and3rson/lilka/docs/keira/lua/reference/lilka.rst

``lilka``: Спеціальні функції
=============================

Цей модуль описує функції, які ви можете визначити в своєму коді, щоб вони викликались автоматично в певних ситуаціях.

Детальніше про їх поведінку можна прочитати в :ref:`секції про написання ігор на Lua <lua-games>`.

.. lua:module:: lilka
    :noindex:

.. lua:function:: init()

    Ця функція автоматично викликається один раз при запуску програми.

    Ви повинні визначити її в своєму коді, якщо ви хочете використовувати її для ініціалізації вашої програми.

.. lua:function:: update(delta)

    :type delta: number
    :param delta: Час, який пройшов з останнього кадру.

    Ця функція автоматично викликається кожен кадр. Тут виконується ігрова логіка. В параметрі delta передається час, який пройшов з останнього кадру.

    Ви повинні визначити її в своєму коді, якщо ви хочете використовувати її для оновлення вашої програми.

.. lua:function:: draw()

    Ця функція автоматично викликається після `lilka.update`. Тут відбувається відображення графіки.

    Ви повинні визначити її в своєму коді, якщо ви хочете використовувати її для малювання вашої програми.

.. lua:autoclass:: lilka

    .. Does not work with aliases... So we have to copy-paste the stuff above.
    .. :members: init, update, draw
