and3rson/lilka/docs/keira/lua/reference/buzzer.rst

``buzzer`` - П'єзо-динамік
--------------------------

Функції для роботи з п'єзо-динаміком.

.. note:: Ці функції не блокують виконання програми: всі звуки та мелодії відтворюються в фоновому режимі.

.. lua:autoclass:: buzzer
