and3rson/lilka/docs/keira/lua/reference/math.rst

``math`` - Арифметичні функції
------------------------------

Цей модуль містить функції для виконання різних арифметичних та тригонометричних операцій.

.. lua:autoclass:: math
