and3rson/lilka/docs/keira/lua/reference/geometry.rst

``geometry`` - Геометричні функції
----------------------------------

Цей модуль містить функції, які будуть корисні для створення ігор, де потрібно працювати з геометричними об'єктами та колізіями.

.. lua:autoclass:: geometry
