and3rson/lilka/docs/keira/lua/reference/state.rst

``state`` - Збереження стану програми
-------------------------------------

.. lua:autoclass:: state
