and3rson/lilka/docs/keira/lua/reference/util.rst

``util`` - Утиліти
------------------

Різні корисні функції.

.. lua:autoclass:: util
