and3rson/lilka/docs/_static/lilka_bottom.png

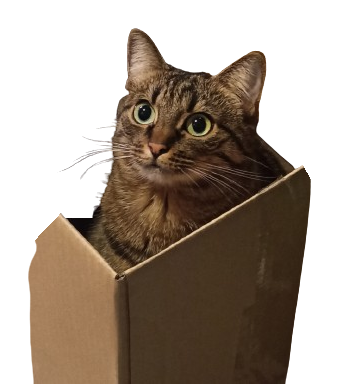
docs/_static/lilka_bottom.png
