and3rson/lilka/docs/_static/lilka_bottom_20.png

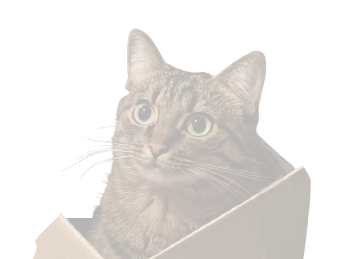
docs/_static/lilka_bottom_20.png
