and3rson/lilka/docs/_static/v2.jpg

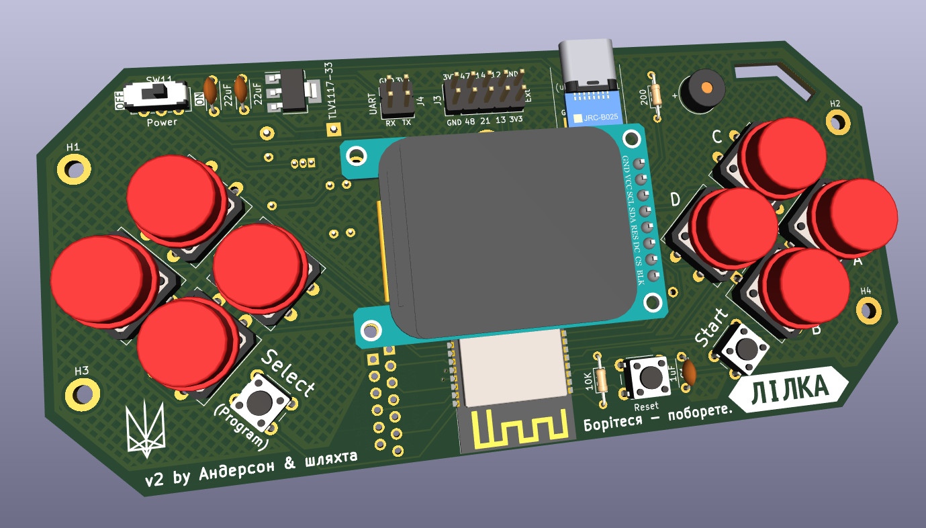
docs/_static/v2.jpg
