and3rson/lilka/docs/keira/images/02_inside_vscode.png

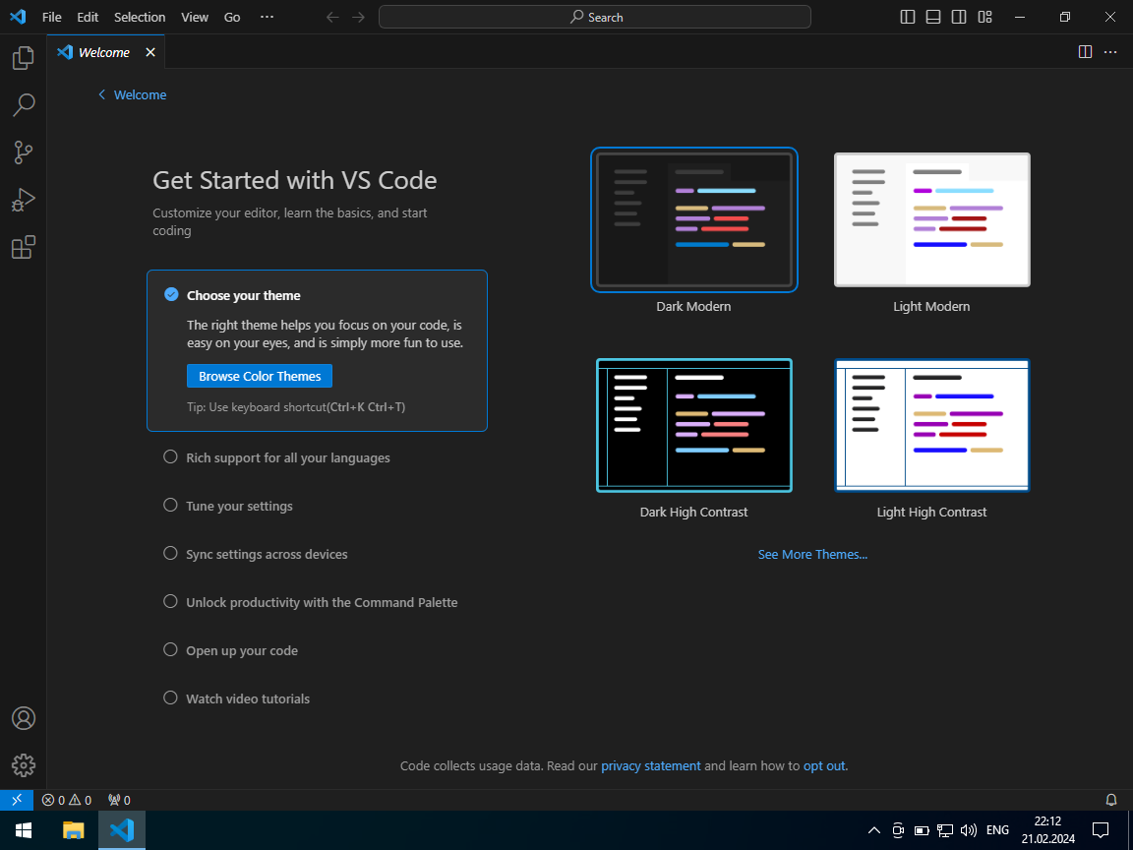
docs/keira/images/02_inside_vscode.png
