and3rson/lilka/docs/keira/images/08_clone_repo.png

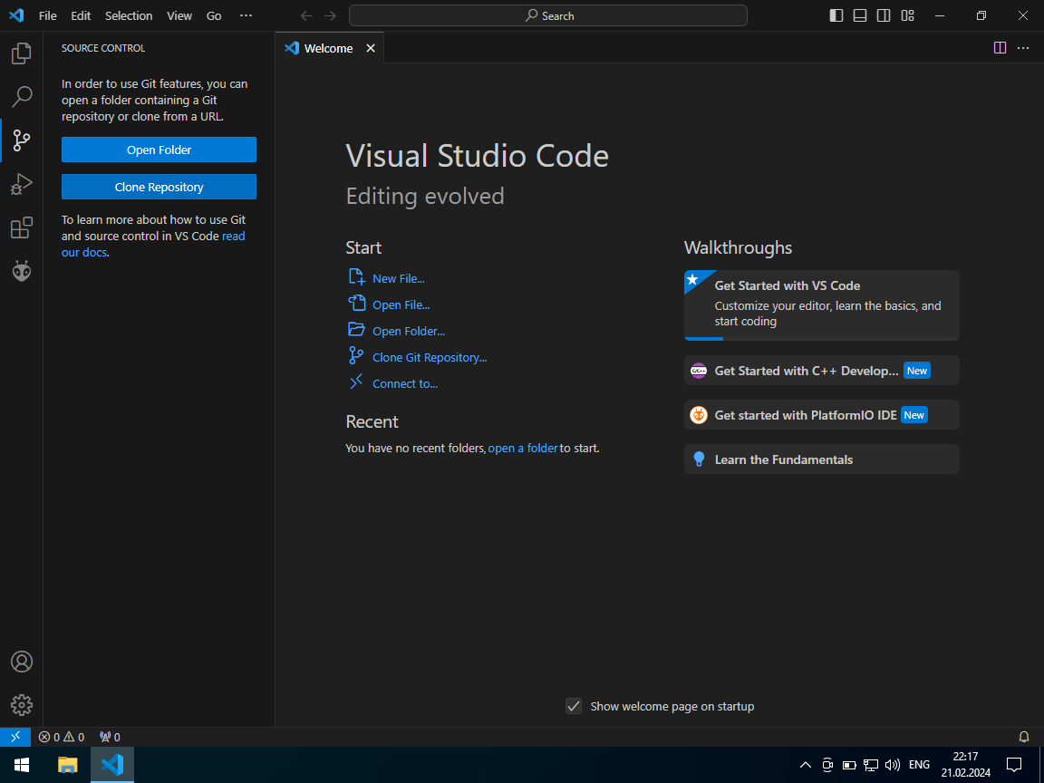
docs/keira/images/08_clone_repo.png
