and3rson/lilka/docs/keira/images/10_see_cloned_repo.png

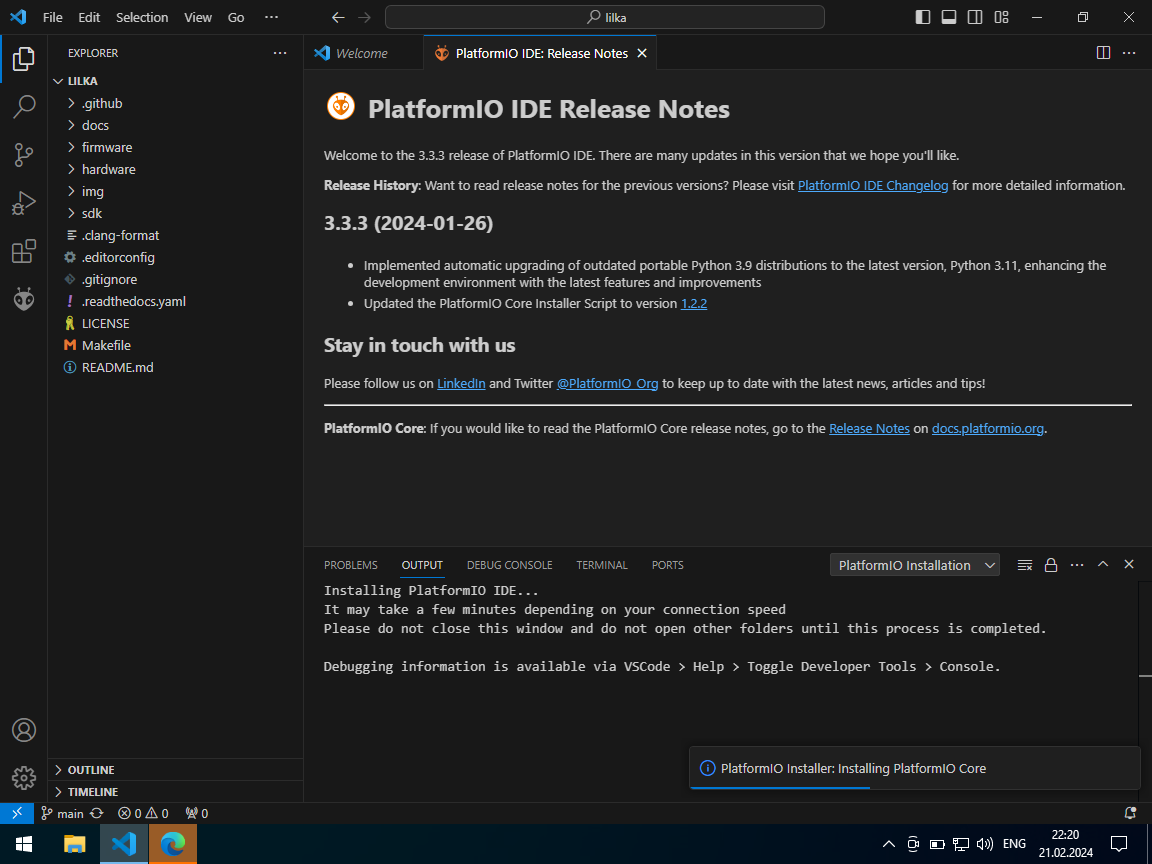
docs/keira/images/10_see_cloned_repo.png
