and3rson/lilka/docs/keira/images/11_open_pio_project.png

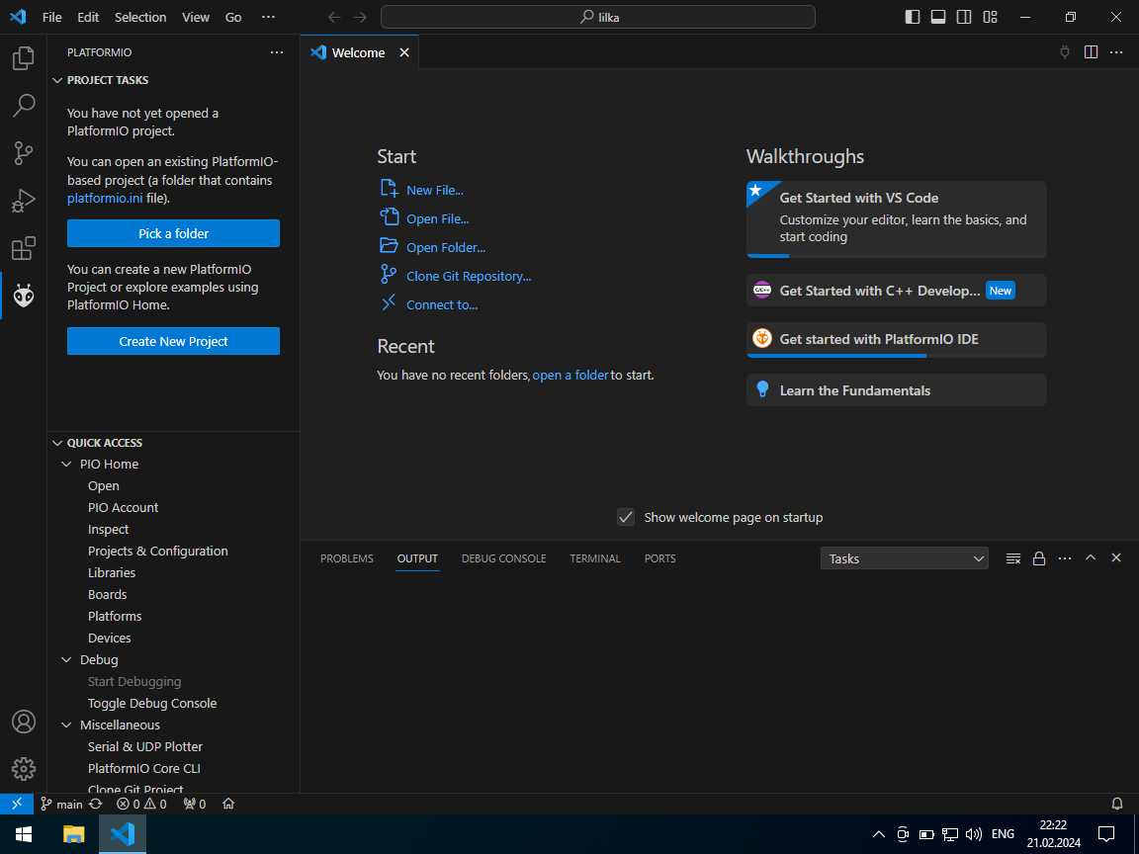
docs/keira/images/11_open_pio_project.png
