and3rson/lilka/docs/keira/images/12_wait_pio_project_init.png

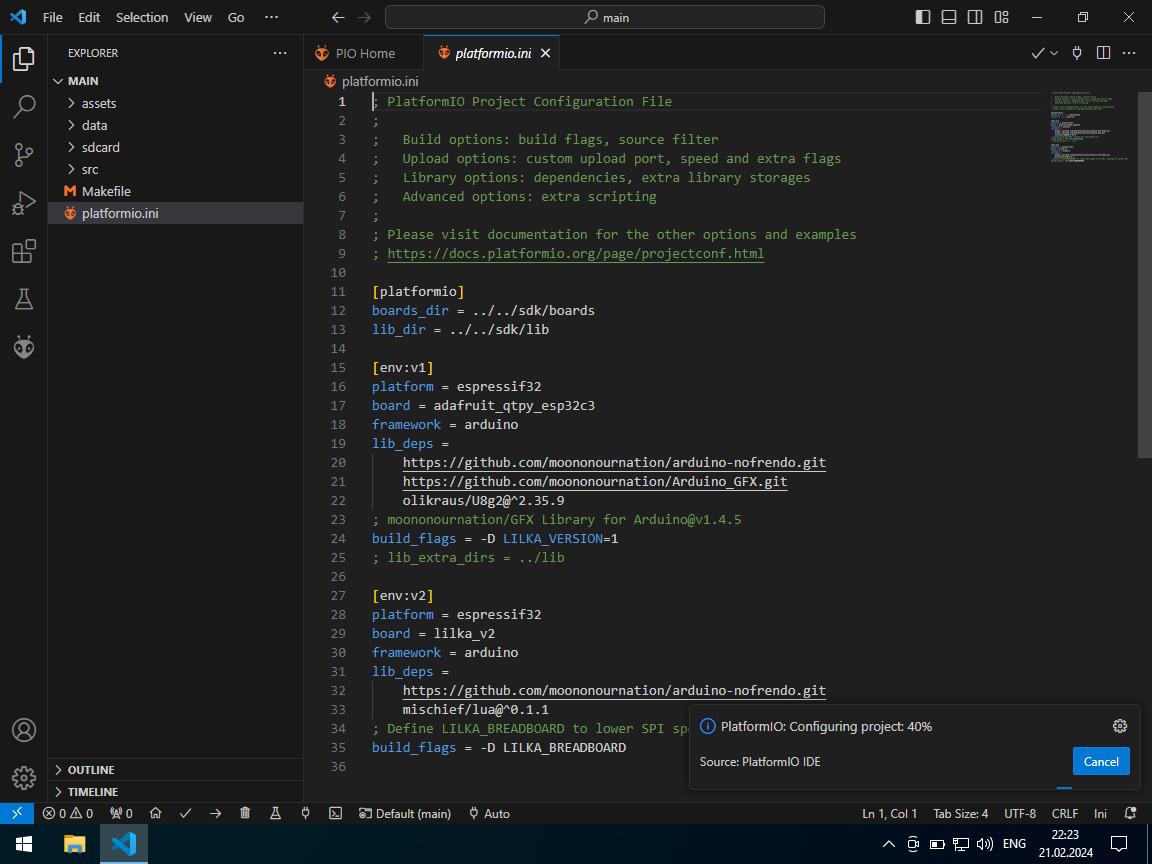
docs/keira/images/12_wait_pio_project_init.png
