and3rson/lilka/docs/keira/images/13_wait_pio_project_init_more.png

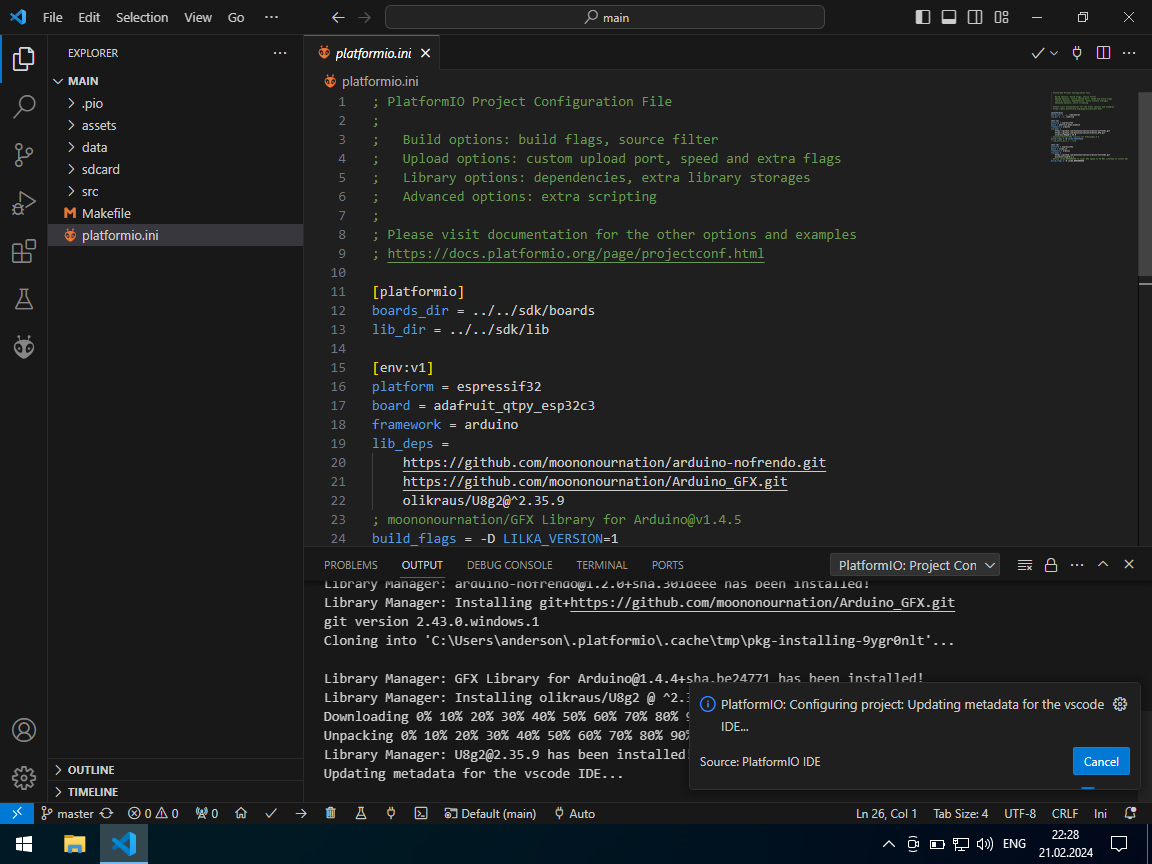
docs/keira/images/13_wait_pio_project_init_more.png
