and3rson/lilka/docs/keira/images/17_run_upload_v2.png

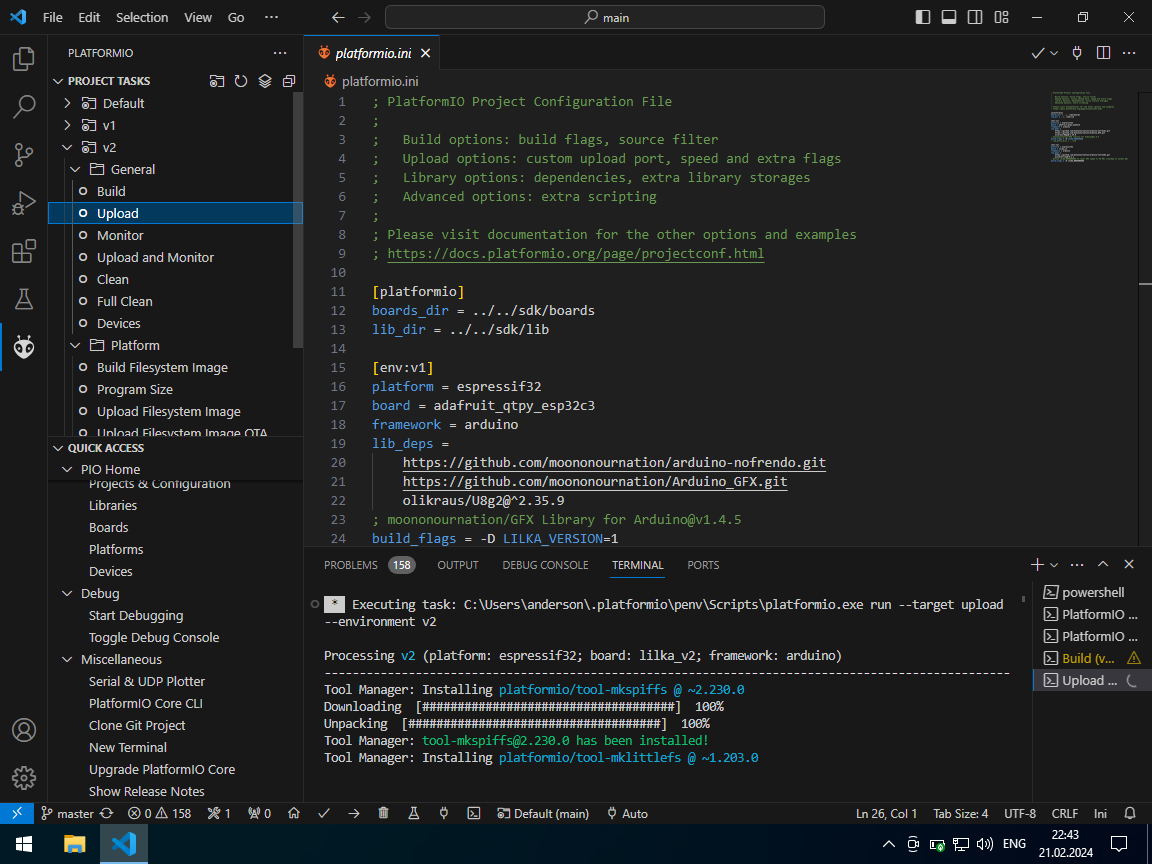
docs/keira/images/17_run_upload_v2.png
