and3rson/lilka/docs/keira/images/18_upload_progress.png

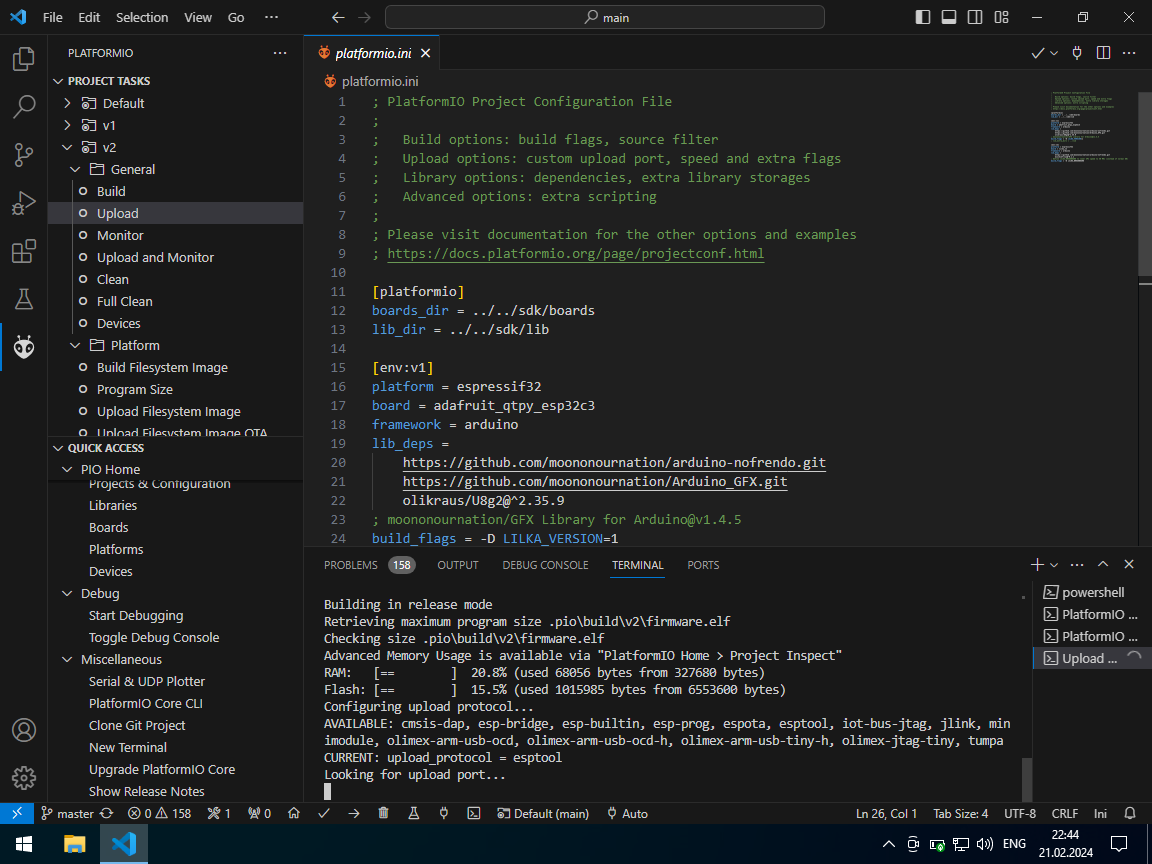
docs/keira/images/18_upload_progress.png
