and3rson/lilka/docs/programming/images/01_download_vscode.png

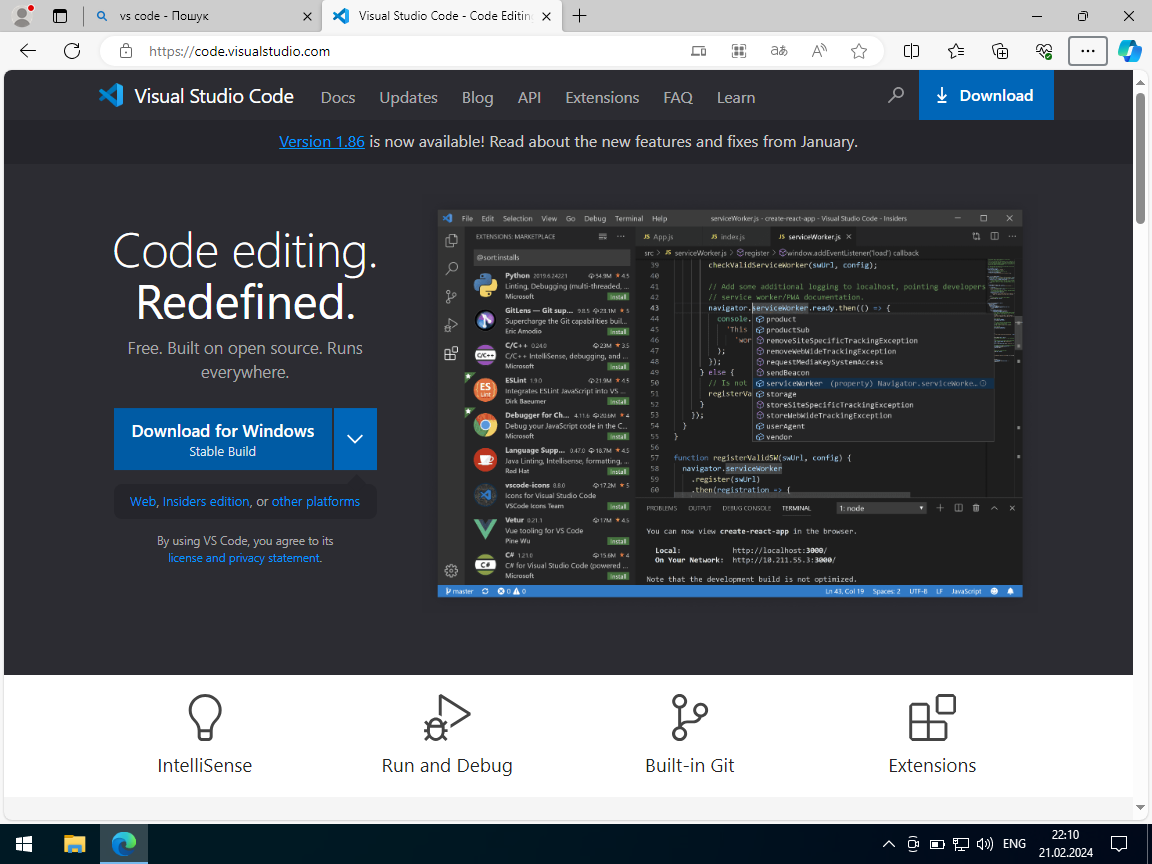
docs/programming/images/01_download_vscode.png
