and3rson/lilka/docs/programming/images/07_use_vs_code_with_git.png

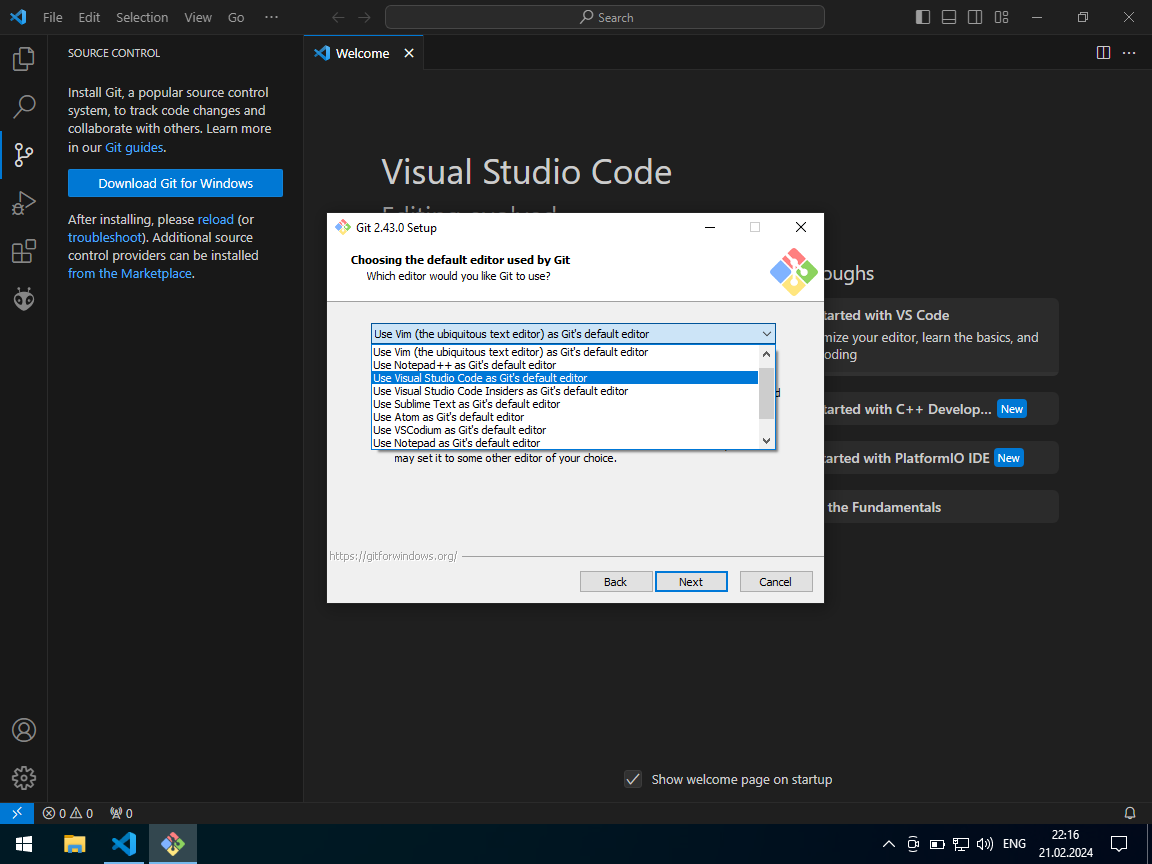
docs/programming/images/07_use_vs_code_with_git.png
