and3rson/lilka/docs/programming/images/custom_firmware/01_pio_new_proj.png

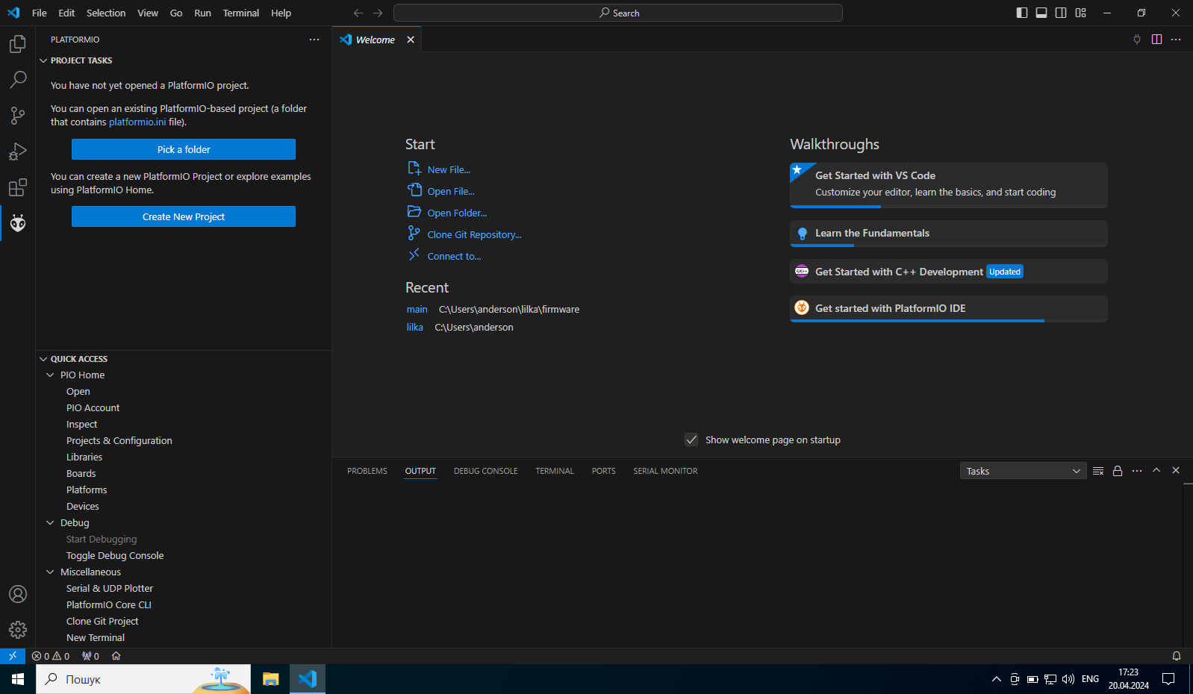
docs/programming/images/custom_firmware/01_pio_new_proj.png
