and3rson/lilka/docs/programming/images/custom_firmware/09_lilka_begin.png

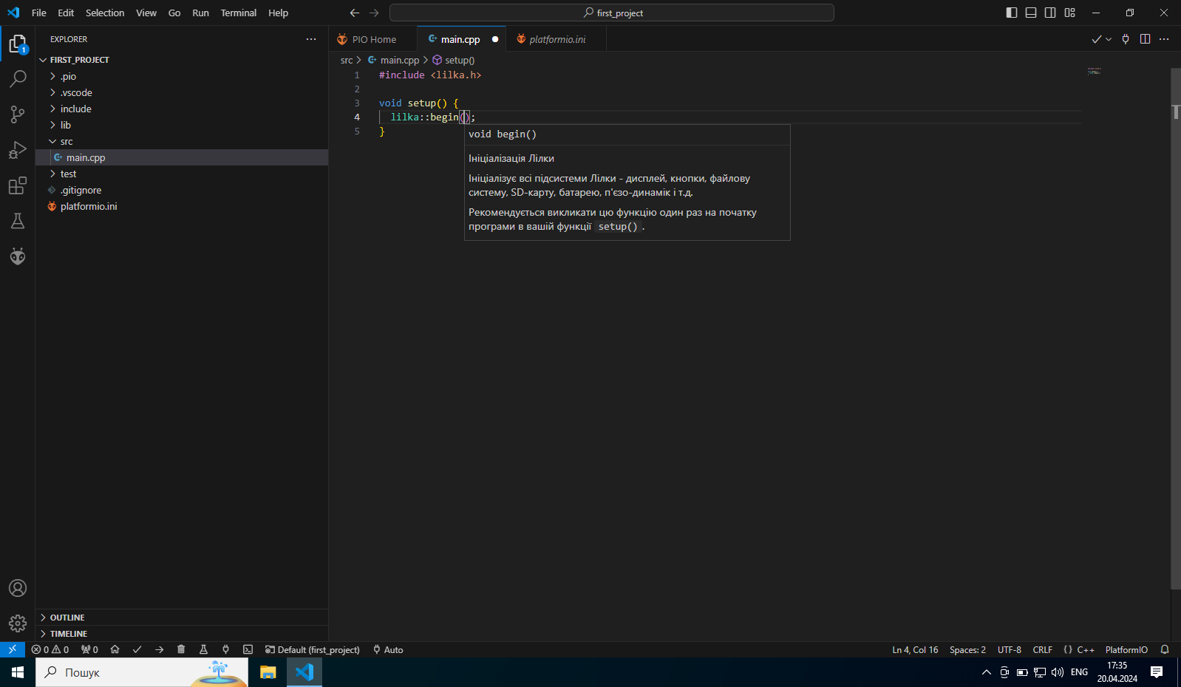
docs/programming/images/custom_firmware/09_lilka_begin.png
