and3rson/lilka/firmware/keira/sdcard/cat/both.bmp

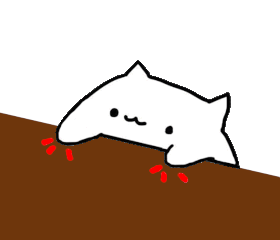
firmware/keira/sdcard/cat/both.bmp
