and3rson/lilka/firmware/keira/sdcard/cat/right.bmp

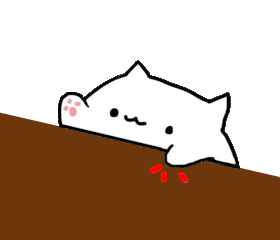
firmware/keira/sdcard/cat/right.bmp
