and3rson/lilka/img/main.png

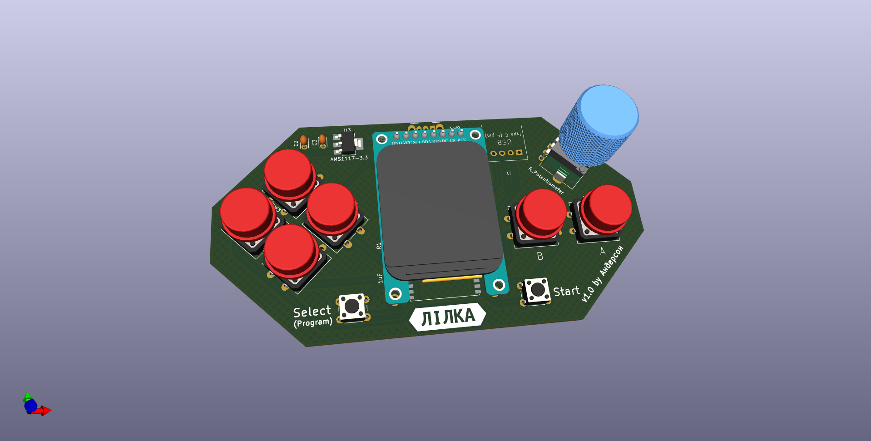
img/main.png
