and3rson/lilka/docs/assembly/images/parts/1n4001.jpg

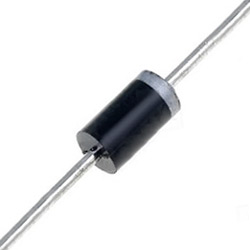
docs/assembly/images/parts/1n4001.jpg
