and3rson/lilka/docs/assembly/images/parts/6mm.jpg

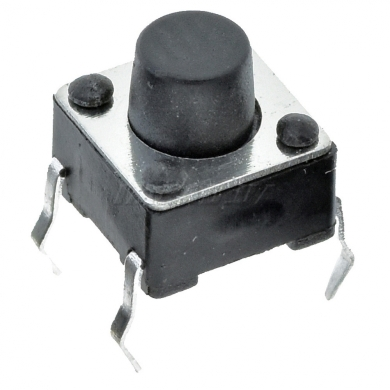
docs/assembly/images/parts/6mm.jpg
