and3rson/lilka/docs/assembly/images/parts/12mm.jpg

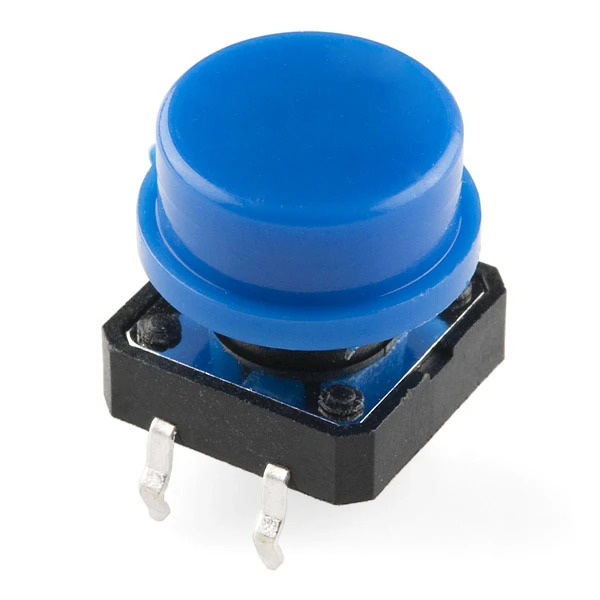
docs/assembly/images/parts/12mm.jpg
