and3rson/lilka/docs/assembly/images/parts/cap.jpg

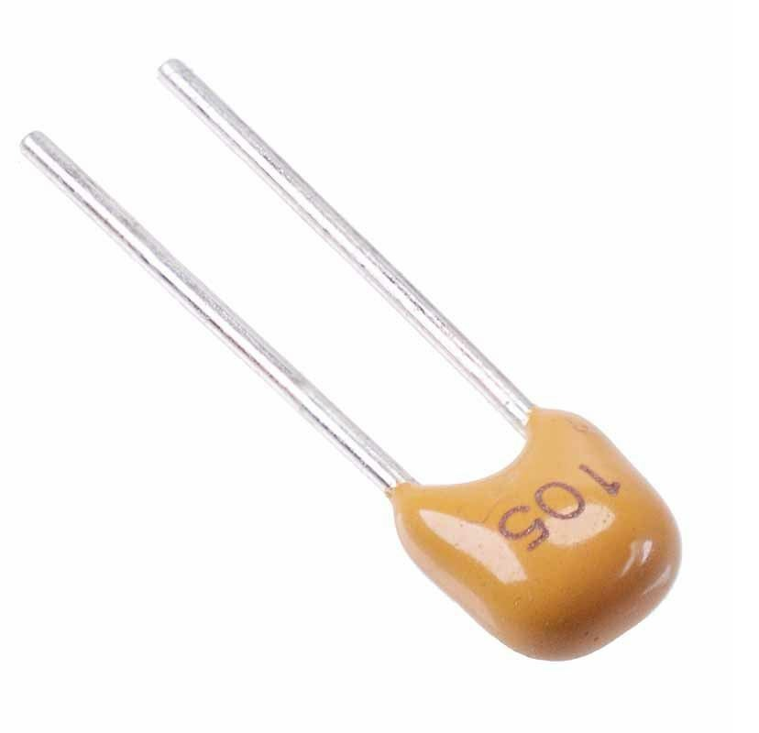
docs/assembly/images/parts/cap.jpg
