and3rson/lilka/docs/assembly/images/parts/display.jpg

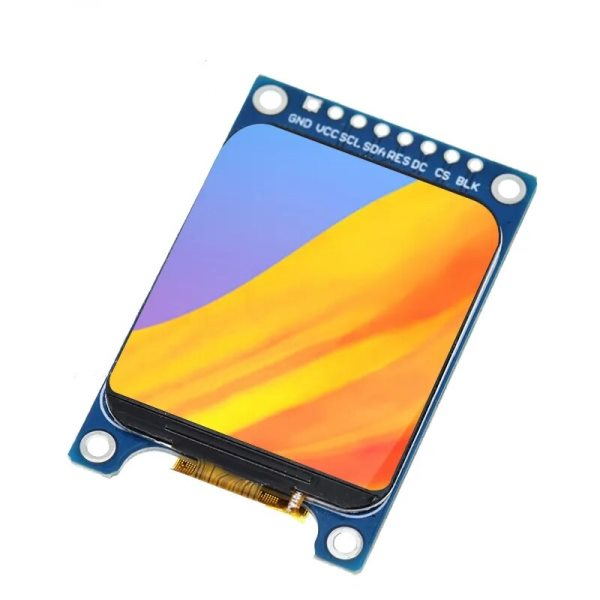
docs/assembly/images/parts/display.jpg
