and3rson/lilka/docs/assembly/images/parts/header.jpg

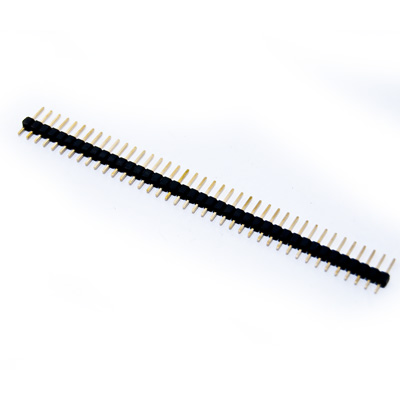
docs/assembly/images/parts/header.jpg
