and3rson/lilka/docs/assembly/images/parts/irlml6401.jpg

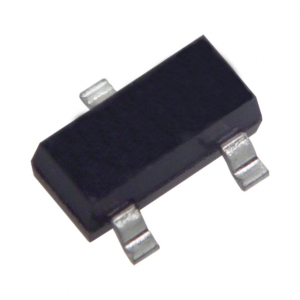
docs/assembly/images/parts/irlml6401.jpg
