and3rson/lilka/docs/assembly/images/parts/lipo.jpg

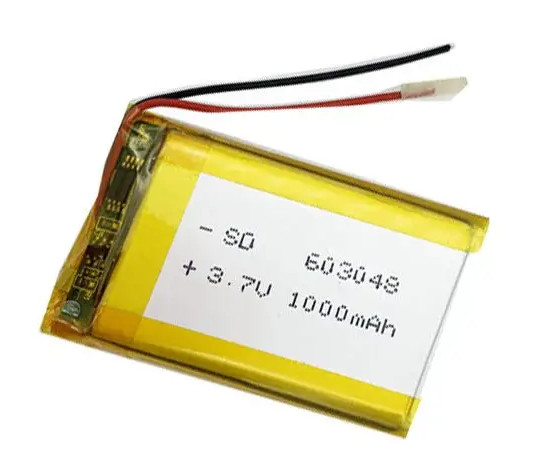
docs/assembly/images/parts/lipo.jpg
