and3rson/lilka/docs/assembly/images/parts/max98357.jpg

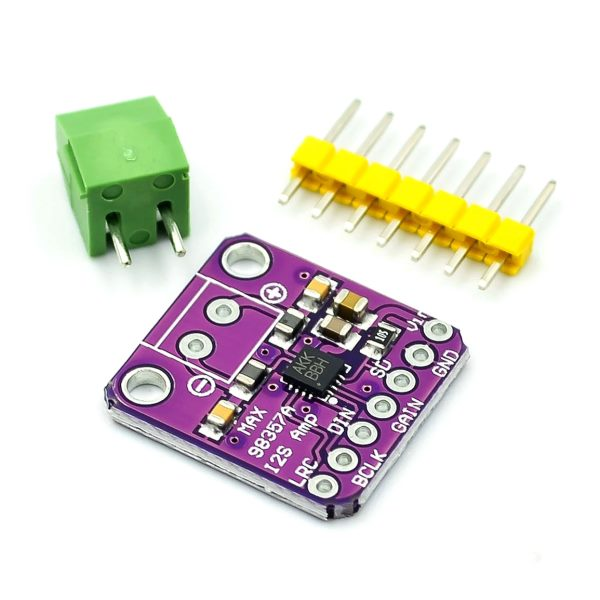
docs/assembly/images/parts/max98357.jpg
