and3rson/lilka/docs/assembly/images/parts/mcu.jpg

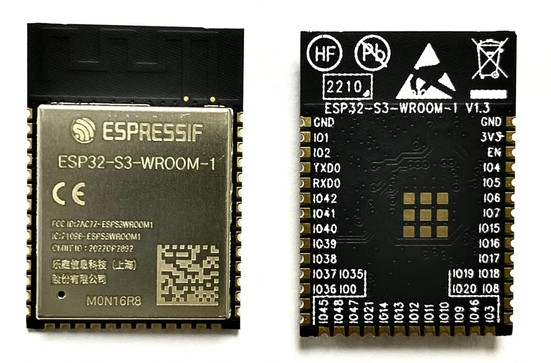
docs/assembly/images/parts/mcu.jpg
