and3rson/lilka/docs/assembly/images/parts/r10k.jpg

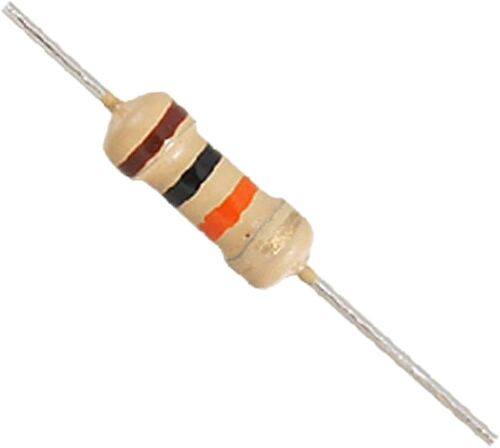
docs/assembly/images/parts/r10k.jpg
