and3rson/lilka/docs/assembly/images/parts/r33k.jpg

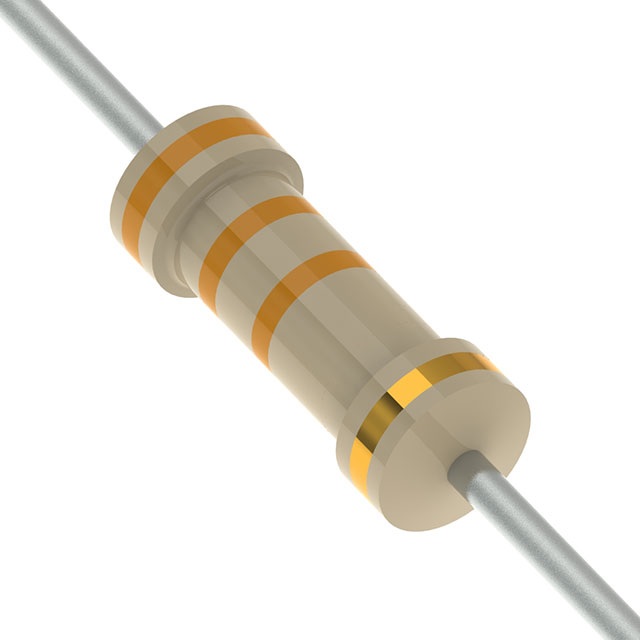
docs/assembly/images/parts/r33k.jpg
