and3rson/lilka/docs/assembly/images/parts/r100k.jpg

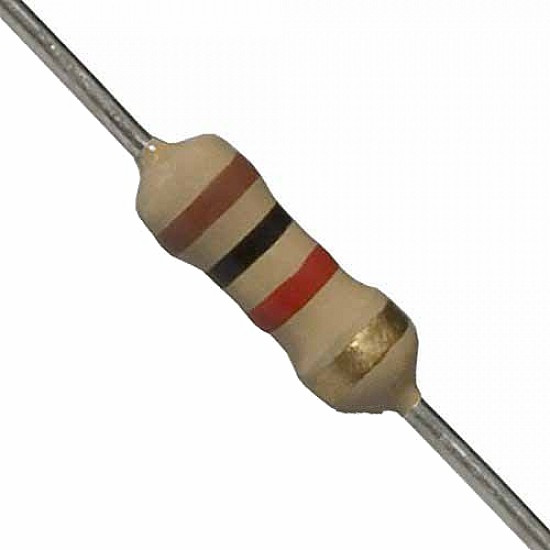
docs/assembly/images/parts/r100k.jpg
