and3rson/lilka/docs/assembly/images/parts/reg.jpg

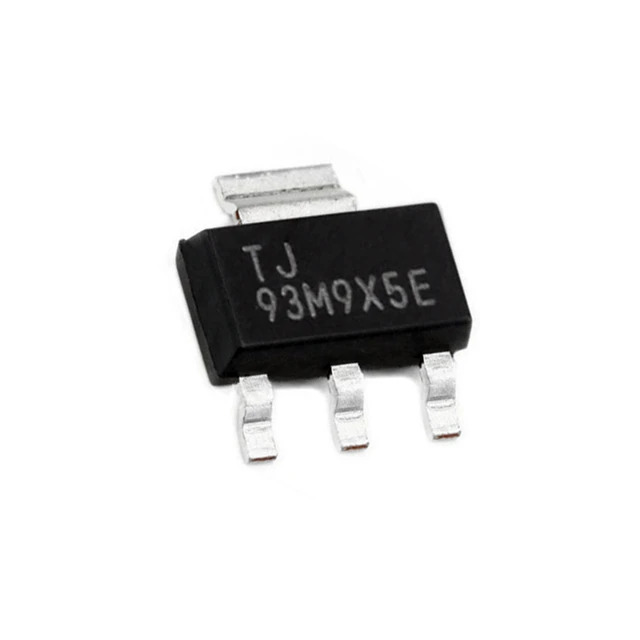
docs/assembly/images/parts/reg.jpg
