and3rson/lilka/docs/assembly/images/parts/sd.jpg

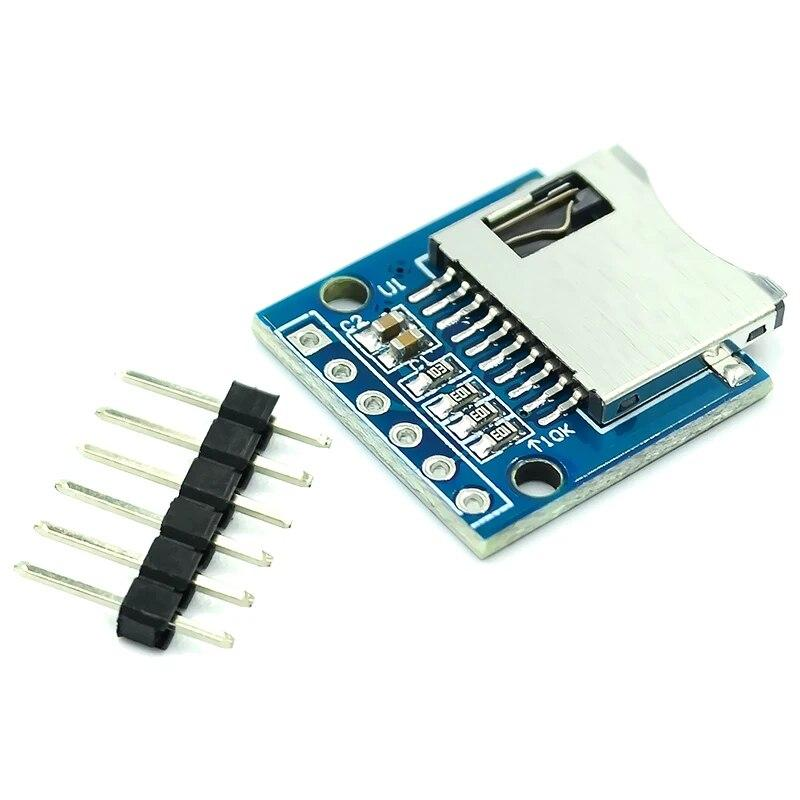
docs/assembly/images/parts/sd.jpg
