and3rson/lilka/docs/assembly/images/parts/socket.jpg

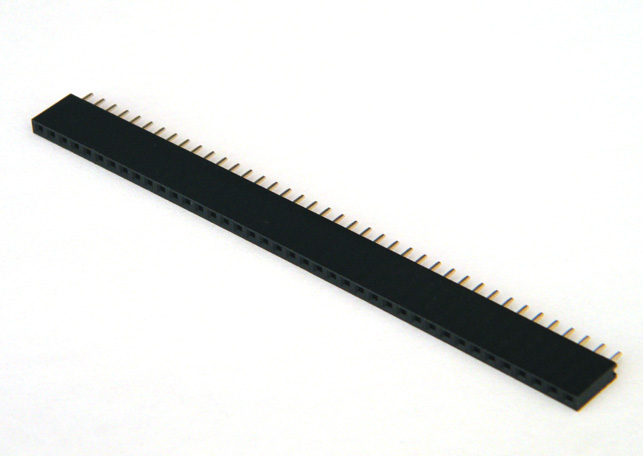
docs/assembly/images/parts/socket.jpg
