and3rson/lilka/docs/assembly/images/parts/speaker.jpg

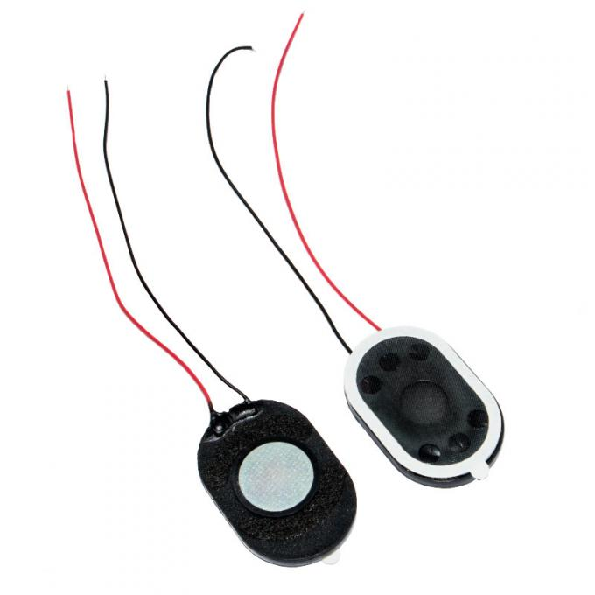
docs/assembly/images/parts/speaker.jpg
