and3rson/lilka/docs/assembly/images/parts/toggle.jpg

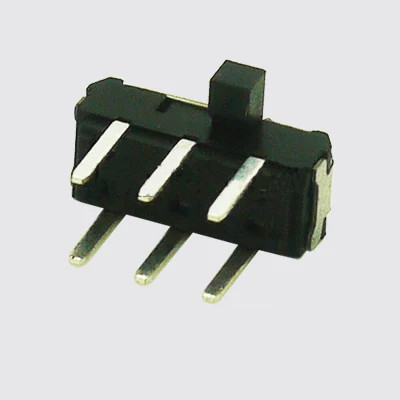
docs/assembly/images/parts/toggle.jpg
