and3rson/lilka/docs/assembly/images/parts/tp4056.jpg

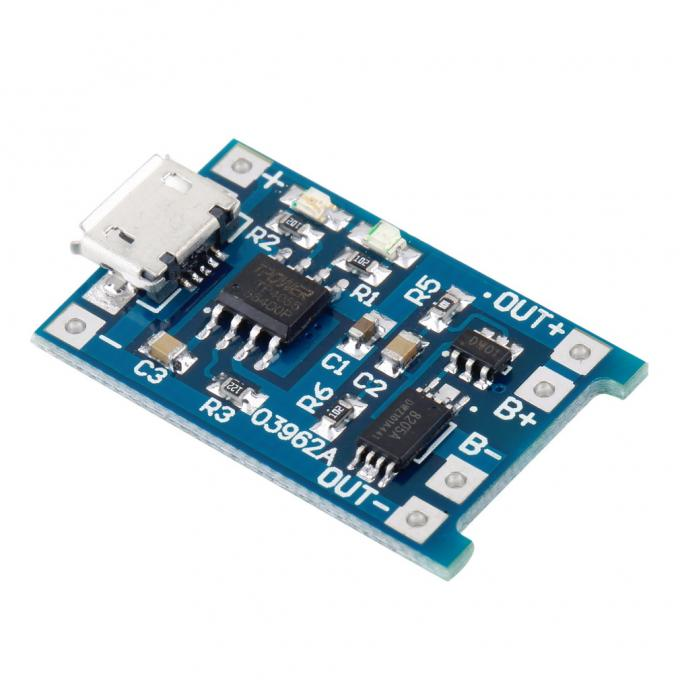
docs/assembly/images/parts/tp4056.jpg
