and3rson/lilka/docs/keira/images/14_pio_build_v2.png

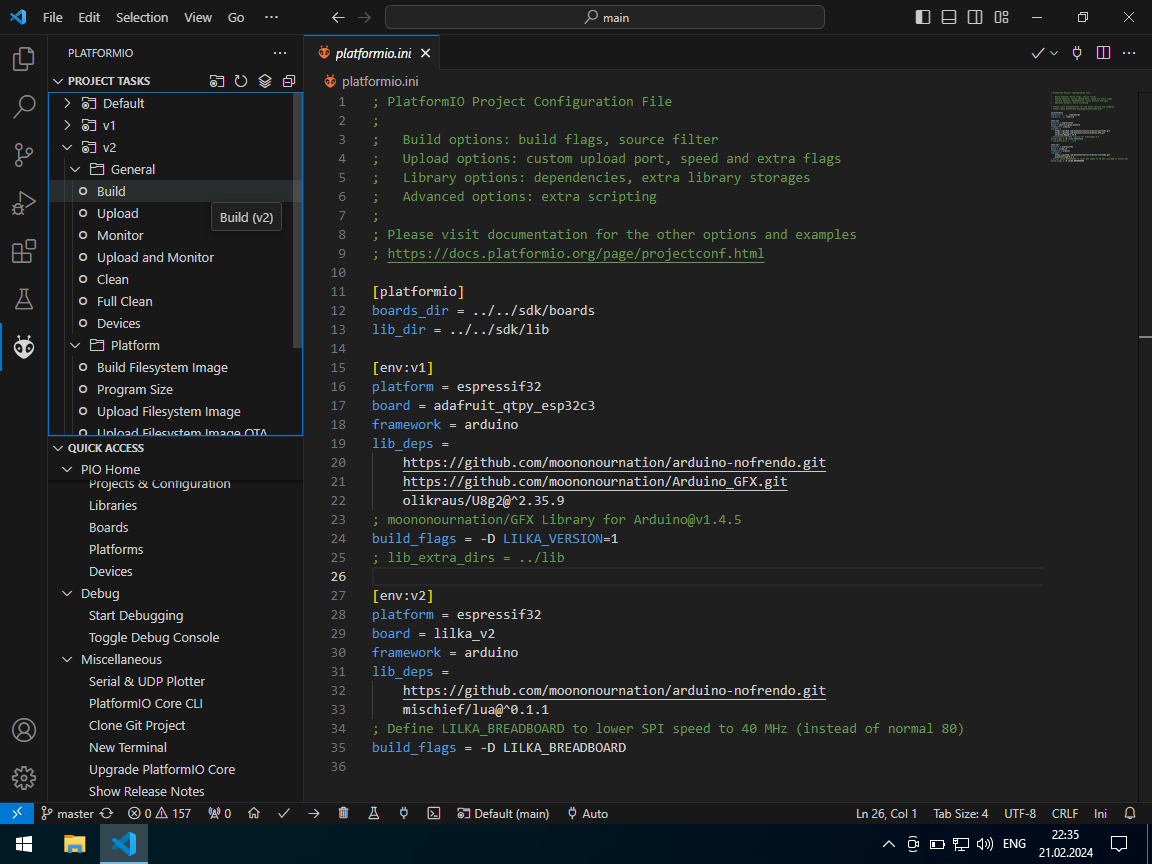
docs/keira/images/14_pio_build_v2.png
