and3rson/lilka/docs/keira/images/15_pio_build_v2_progress.png

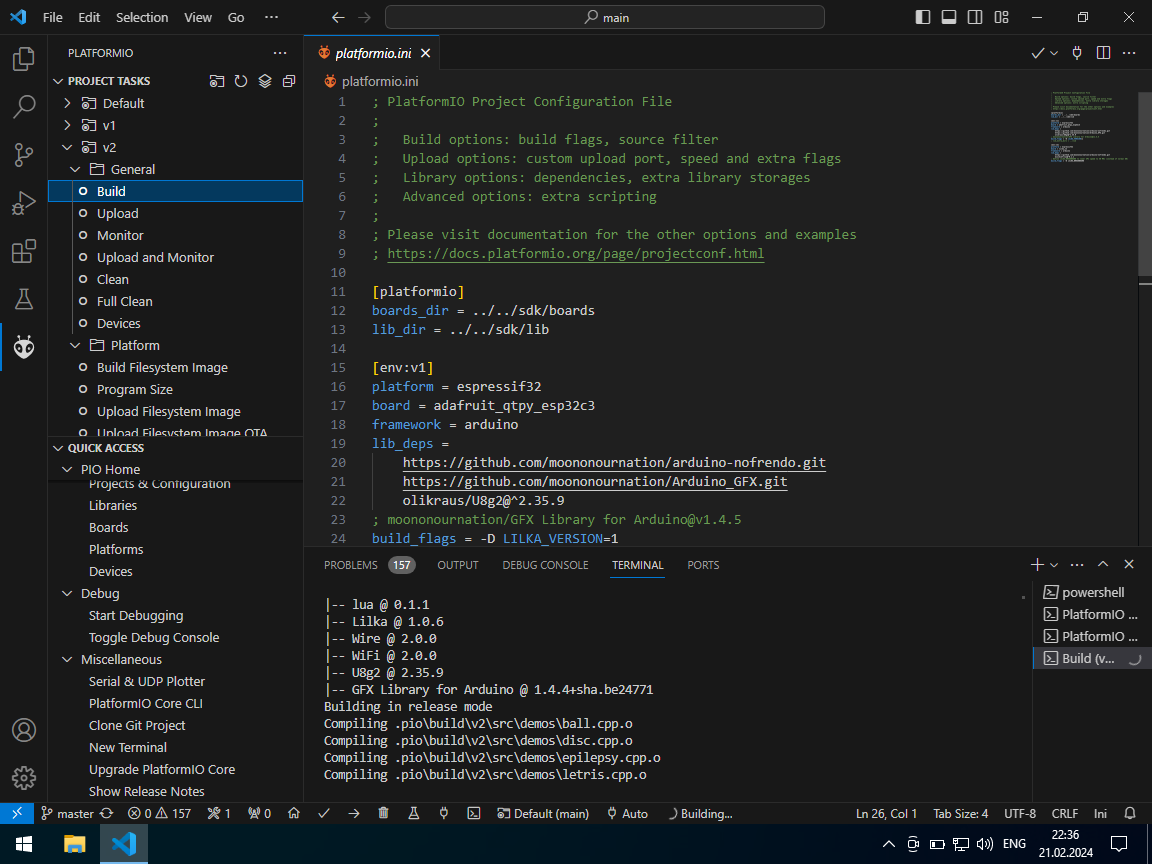
docs/keira/images/15_pio_build_v2_progress.png
