and3rson/lilka/docs/programming/images/04_install_platformio.png

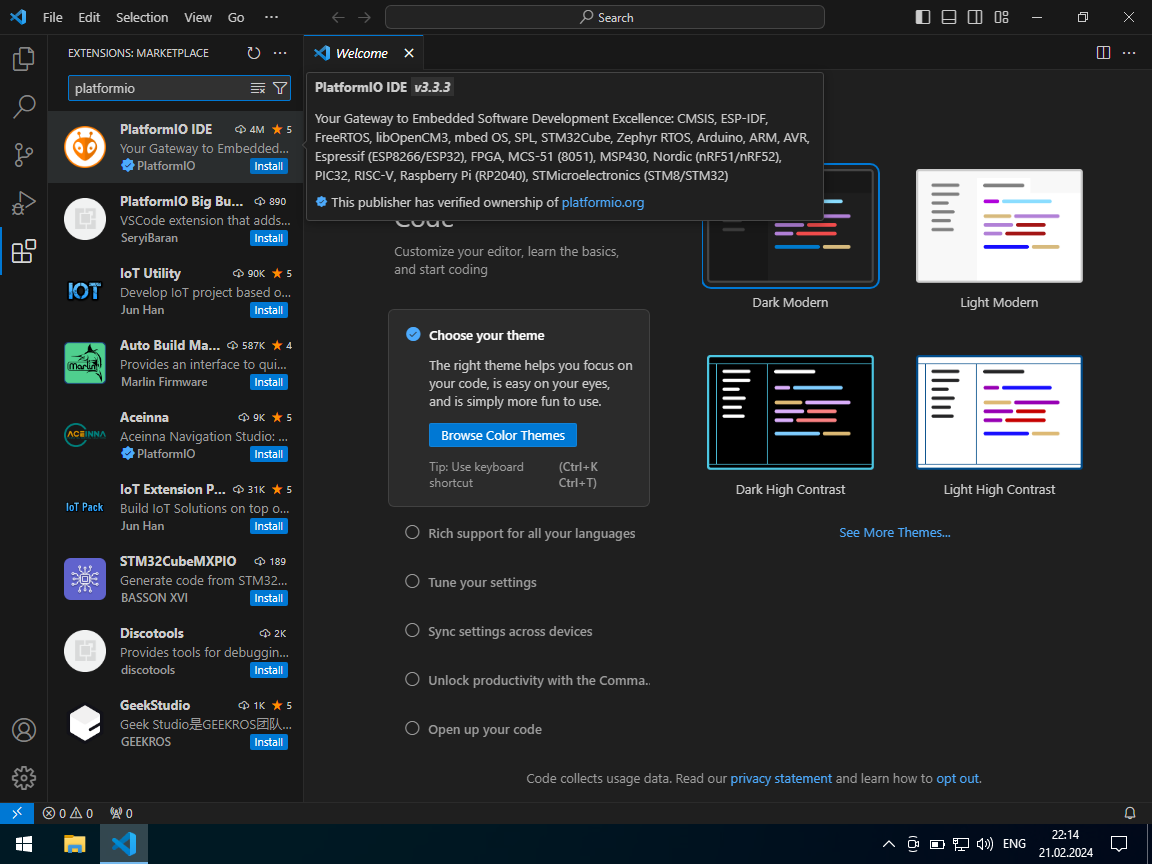
docs/programming/images/04_install_platformio.png
