and3rson/lilka/docs/programming/images/custom_firmware/07_install_lilka_lib.png

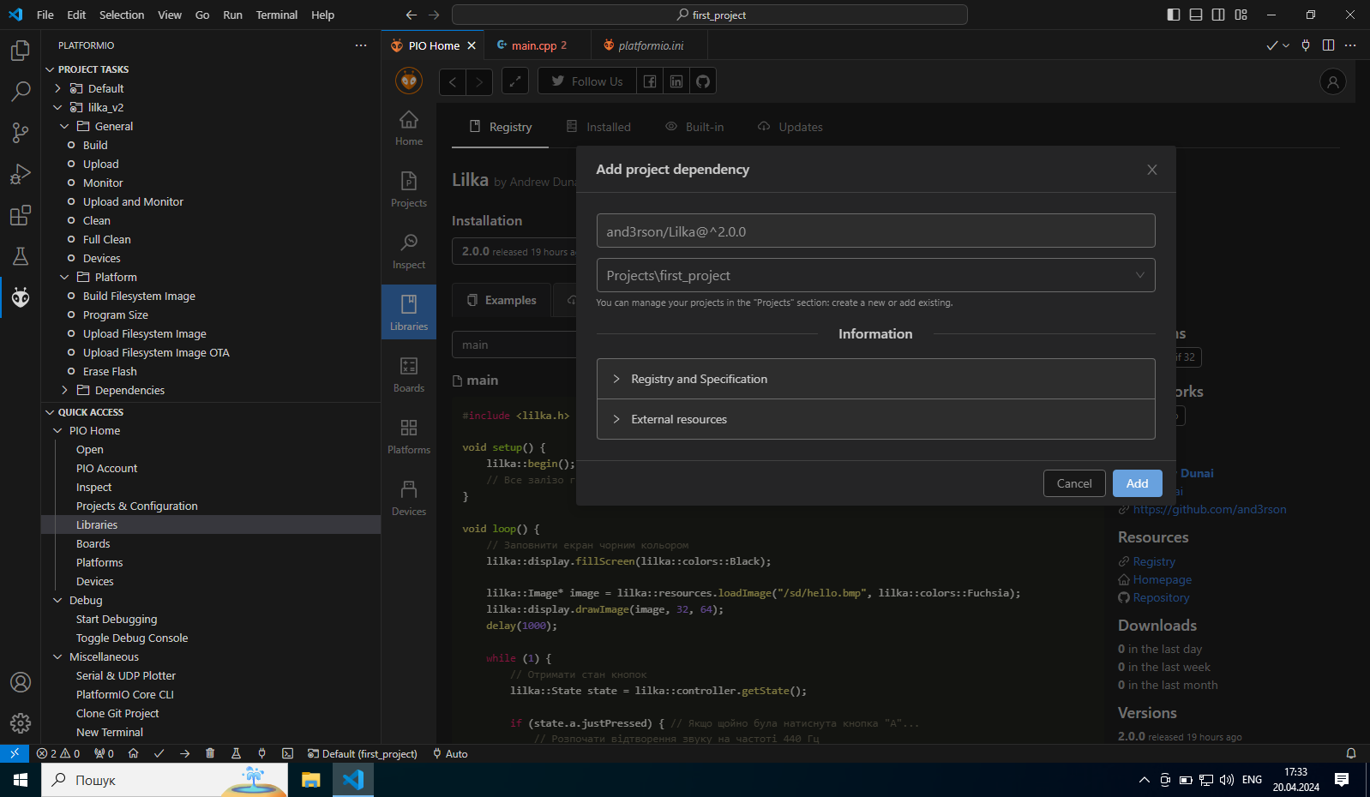
docs/programming/images/custom_firmware/07_install_lilka_lib.png
