and3rson/lilka/docs/programming/images/custom_firmware/11_start_build.png

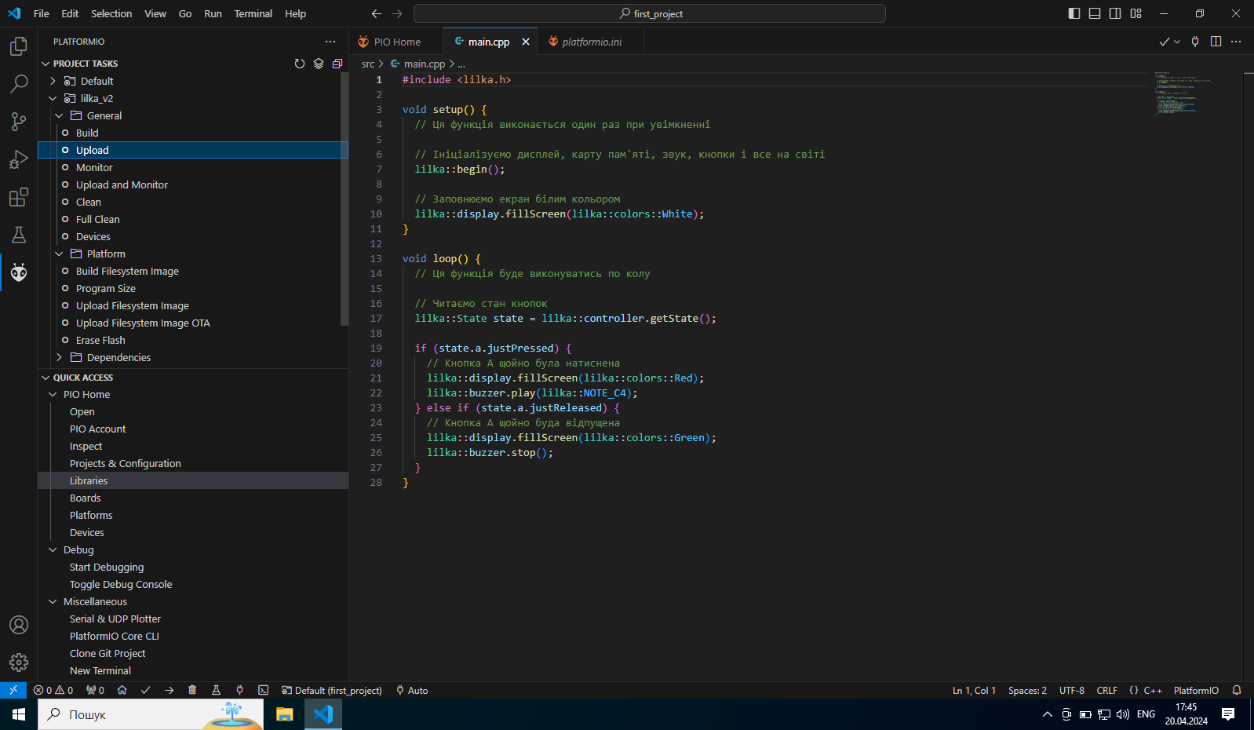
docs/programming/images/custom_firmware/11_start_build.png
