and3rson/lilka/firmware/keira/src/apps/tamagotchi/hardcoded_state.h

static const uint8_t hardcodedState[] PROGMEM = {
    0xB4, 0x04, 0x6D, 0x00, 0x2D, 0x00, 0x00, 0x01, 0x04, 0xF9, 0x0B, 0x77, 0x3C, 0xFC, 0xBC, 0x00, 0x00, 0xFC, 0xBC,
    0x5C, 0x3C, 0xFC, 0xBC, 0x01, 0x01, 0x07, 0x02, 0x00, 0x00, 0x00, 0xC2, 0x03, 0x00, 0x01, 0x00, 0x0C, 0x00, 0x00,
    0x00, 0x0A, 0x00, 0x00, 0x00, 0x08, 0x07, 0x00, 0x00, 0x06, 0x00, 0x00, 0x00, 0x04, 0x00, 0x08, 0x00, 0x02, 0x01,
    0x30, 0xE0, 0x53, 0x38, 0x00, 0x00, 0x00, 0x63, 0x54, 0xC0, 0x00, 0x00, 0x00, 0x00, 0x00, 0x00, 0x00, 0xEA, 0x00,
    0x00, 0x00, 0x00, 0x18, 0xF9, 0x75, 0x80, 0xD7, 0xFA, 0x09, 0xF0, 0x80, 0xFC, 0xF0, 0x00, 0x62, 0x70, 0x0F, 0x00,
    0x00, 0xF6, 0x00, 0x50, 0x08, 0x0F, 0x70, 0x0A, 0x10, 0x00, 0x13, 0xAC, 0x00, 0x01, 0xB9, 0x01, 0x10, 0xC0, 0x01,
    0xF0, 0x8A, 0x00, 0x0F, 0xFF, 0x50, 0x10, 0x50, 0x80, 0x00, 0x00, 0x00, 0x00, 0x00, 0xFF, 0xC1, 0xFF, 0xC1, 0xD1,
    0xFF, 0xD1, 0xFF, 0x00, 0xF7, 0x05, 0xB2, 0xF3, 0x00, 0x00, 0x00, 0x00, 0x00, 0x00, 0x00, 0x00, 0x00, 0x00, 0x00,
    0x00, 0x00, 0x00, 0x00, 0x00, 0x00, 0x00, 0x00, 0x00, 0x00, 0x77, 0x4B, 0x17, 0x77, 0x17, 0x71, 0x01, 0x07, 0x71,
    0x77, 0x1D, 0x70, 0x00, 0x21, 0x77, 0x1A, 0xE1, 0x78, 0x44, 0x50, 0x24, 0x50, 0x00, 0x00, 0x00, 0x00, 0x00, 0x00,
    0x00, 0x00, 0x00, 0x00, 0x00, 0x00, 0x00, 0x00, 0x00, 0x00, 0x00, 0x00, 0x00, 0x00, 0x00, 0x00, 0x00, 0x00, 0x00,
    0x00, 0x00, 0x00, 0x00, 0x00, 0x00, 0x00, 0x00, 0x00, 0x00, 0x00, 0x00, 0x00, 0x00, 0x00, 0x00, 0x00, 0x00, 0x00,
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
0xDD,0x44,0x30,0x00,0x00,0x00,0x00,0x00,0x00,0x00,0x00,0x00,0x00,0x00,0x00,0x00,
0x90,0x51,0xB4,0x55,0x49,0x2C,0x02,0x99,0x46,0x56,0x08,0x11,0x00,0x00,0x00,0x00,
0x00,0x00,0x00,0x00,0x00,0x00,0x00,0x00,0x00,0x00,0x00,0x00,0x00,0x00,0x00,0x00,
0x70,0x00,0x00,0x00,0x00,0x00,0x00,0x00,};
*/
