and3rson/lilka/firmware/keira/src/apps/tamagotchi/rom_12bit.h

static const unsigned char g_program_b12[] PROGMEM = {
    0xFA, 0x2C, 0x87, 0xE1, 0x0A, 0x80, 0xA8, 0x0A, 0x95, 0x51, 0x2E, 0x50, 0x02, 0x0F, 0xC4, 0xFC, 0x5F, 0xC6, 0xFC,
    0x05, 0xEF, 0xB7, 0xDE, 0x2F, 0xF4, 0x80, 0x1A, 0xFC, 0x4F, 0xC5, 0xFC, 0x6F, 0xC0, 0x5E, 0xFB, 0x7D, 0xE2, 0x0F,
    0x57, 0xFD, 0x0F, 0xD6, 0xFD, 0x5F, 0xD4, 0xFD, 0xFB, 0x02, 0x53, 0xCE, 0x00, 0xE8, 0x0B, 0x26, 0x51, 0x2E, 0xE2,
    0xEC, 0x6E, 0x60, 0x50, 0x9E, 0xE8, 0xEC, 0x9F, 0xDF, 0xE0, 0x0E, 0x90, 0x82, 0x25, 0x12, 0xEA, 0xBE, 0xF0, 0xEA,
    0x75, 0x09, 0xFD, 0xFE, 0x00, 0xE9, 0x08, 0x23, 0xEC, 0x38, 0x22, 0xAD, 0x3F, 0xDF, 0x42, 0xC4, 0x35, 0x73, 0xDF,
    0xDF, 0x5E, 0xFB, 0x2A, 0x90, 0x0E, 0x01, 0xE1, 0x0E, 0x80, 0xB0, 0x09, 0x00, 0x90, 0x09, 0x00, 0x90, 0x09, 0x00,
    0x90, 0x09, 0x00, 0x90, 0x0C, 0x1F, 0x74, 0x7F, 0xDF, 0xE4, 0x44, 0x86, 0xE4, 0x44, 0x00, 0x5E, 0xFB, 0x2A, 0xE9,
    0xAE, 0xE0, 0xE9, 0x6E, 0x01, 0xE9, 0x0E, 0x0E, 0xE8, 0x0B, 0x00, 0x48, 0xDF, 0x5E, 0xA2, 0x7B, 0x80, 0x48, 0xDF,
    0x5E, 0xA2, 0x8B, 0x12, 0x48, 0xDF, 0x5E, 0xA2, 0x7B, 0x92, 0x48, 0xDF, 0x5E, 0xA2, 0x8B, 0x48, 0xF4, 0x14, 0x9F,
    0xB3, 0xEF, 0x41, 0x4A, 0x7F, 0x5E, 0xA2, 0x7B, 0xC8, 0xF4, 0x14, 0x9F, 0xBB, 0xEF, 0x41, 0x4A, 0x7F, 0x5E, 0xA2,
    0x8B, 0x36, 0xF4, 0x14, 0xA3, 0xB2, 0xEF, 0x41, 0x4A, 0x3F, 0x5E, 0xA2, 0x7B, 0xB6, 0xF4, 0x14, 0xA3, 0xBA, 0xEF,
    0x41, 0x0A, 0x34, 0x8F, 0xEE, 0x0E, 0xFB, 0xEE, 0x0E, 0xFB, 0xEE, 0x0E, 0xFB, 0xEE, 0x0E, 0xFB, 0xEE, 0x0E, 0xFB,
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
    0xE8, 0xFD, 0xFE, 0x0F, 0xE8, 0x0B, 0x73, 0xE2, 0x6F, 0xFB, 0xEC, 0x2E, 0x20, 0xC8, 0x8F, 0xDF, 0xB7, 0x5E, 0x60,
    0xEE, 0x8E, 0xE9, 0xB5, 0x7E, 0xE9, 0x52, 0x1F, 0xDF, 0xC0, 0x1C, 0x50, 0xDD, 0x12, 0xFD, 0x7F, 0xBD, 0xC8, 0x2F,
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
};
