and3rson/lilka/firmware/keira/src/apps/liltracker/liltracker.h

#pragma once

#include "app.h"
#include "sequencer.h"

class LilTrackerApp : public App {
public:
    LilTrackerApp();
    explicit LilTrackerApp(String path);

private:
    Sequencer sequencer;
    void run() override;
    int drawElement(
        const char* text, int16_t x, int16_t y, lilka::Alignment hAlign, lilka::Alignment vAlign, bool editing,
        bool focused, uint16_t color
    );
    // void startPreview(Track* track, page_t* page, int8_t requestedChannelIndex, uint16_t requestedEventIndex);
    void alert(String title, String message);
    bool confirm(String title, String message);
    String filePicker(String ext, bool isSave);
    void loadTrack(Track* track, String path);
    void saveTrack(Track* track, String path);

    String initialPath;
};
