and3rson/lilka/firmware/keira/src/apps/tamagotchi/bitmaps.h

#include <sys/_stdint.h>
static const uint8_t bitmaps[] PROGMEM = {
    0x00, 0x0c, 0x00, 0x00, 0x00, 0x0c, 0x00, 0x00, 0x00, 0x03, 0x00, 0x00, 0x00, 0x03, 0x00, 0x00, 0xfc, 0xff, 0x00,
    0x00, 0xfc, 0xff, 0x00, 0x00, 0xcf, 0xff, 0x03, 0x00, 0xcf, 0xff, 0x03, 0x00, 0xf3, 0xff, 0x03, 0x00, 0xf3, 0xff,
    0x03, 0x00, 0xff, 0xff, 0x03, 0x00, 0xff, 0xff, 0x03, 0x00, 0xff, 0xff, 0x03, 0x00, 0xff, 0xff, 0x03, 0x00, 0xfc,
    0xff, 0x00, 0x00, 0xfc, 0xff, 0x00, 0x00, 0xf0, 0x3c, 0x00, 0x00, 0xf0, 0x3c, 0x00, 0x00, 0x00, 0x03, 0x00, 0x00,
    0x00, 0x03, 0x00, 0x00, 0x0c, 0xc0, 0x00, 0x00, 0x0c, 0xc0, 0x00, 0x00, 0xc0, 0x0f, 0x00, 0x00, 0xc0, 0x0f, 0x00,
    0x00, 0xf0, 0x3f, 0x00, 0x00, 0xf0, 0x3f, 0x00, 0x00, 0xf3, 0x3f, 0x03, 0x00, 0xf3, 0x3f, 0x03, 0x00, 0xf0, 0x3f,
    0x00, 0x00, 0xf0, 0x3f, 0x00, 0x00, 0xc0, 0x0f, 0x00, 0x00, 0xc0, 0x0f, 0x00, 0x00, 0x0c, 0xc0, 0x00, 0x00, 0x0c,
    0xc0, 0x00, 0x00, 0x00, 0x03, 0x00, 0x00, 0x00, 0x03, 0x00, 0x00, 0x30, 0x00, 0x00, 0x00, 0x30, 0x00, 0x00, 0x00,
    0x3c, 0x00, 0x00, 0x00, 0x3c, 0x00, 0x00, 0x00, 0xff, 0xff, 0x03, 0x00, 0xff, 0xff, 0x03, 0x00, 0x3c, 0x00, 0x00,
    0x00, 0x3c, 0x00, 0x00, 0x00, 0x30, 0x30, 0x00, 0x00, 0x30, 0x30, 0x00, 0x00, 0x00, 0xf0, 0x00, 0x00, 0x00, 0xf0,
    0x00, 0x00, 0xff, 0xff, 0x03, 0x00, 0xff, 0xff, 0x03, 0x00, 0x00, 0xf0, 0x00, 0x00, 0x00, 0xf0, 0x00, 0x00, 0x00,
    0x30, 0x00, 0x00, 0x00, 0x30, 0x00, 0x00, 0xfc, 0xfc, 0x00, 0x00, 0xfc, 0xfc, 0x00, 0x00, 0x03, 0x03, 0x03, 0x00,
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
  0b00010100, 0b00000000,
  0b00001000, 0b00000000,

  0b00000100, 0b00000000,
  0b01000000, 0b00000000,
  0b00011001, 0b00000000,
  0b00111000, 0b00000000,
  0b00100110 ,0b00000000,
  0b01111111, 0b00000000,
  0b01111111, 0b00000000,
  0b11110001, 0b10000000,
  0b11111111, 0b10000000,

  0b00111000, 0b00000000,
  0b01000100, 0b00000000,
  0b10000010, 0b00000000,
  0b10000010, 0b00000000,
  0b10000010, 0b00000000,
  0b01000100, 0b00000000,
  0b00111010, 0b00000000,
  0b00000001, 0b00000000,
  0b00000000, 0b10000000,

  0b01111000, 0b00000000,
  0b11111100, 0b00000000,
  0b11001100, 0b00000000,
  0b11110100, 0b00000000,
  0b11111110, 0b00000000,
  0b11111100, 0b10000000,
  0b11111001, 0b00000000,
  0b01111100, 0b10000000,
  0b00110000, 0b00000000,

  0b00111110, 0b00000000,
  0b01000001, 0b00000000,
  0b10001000, 0b10000000,
  0b10001000, 0b10000000,
  0b10001000, 0b10000000,
  0b10000000, 0b10000000,
  0b10001000, 0b10000000,
  0b01000001, 0b00000000,
  0b00111110, 0b00000000,
};
*/
