and3rson/lilka/firmware/keira/src/apps/lilcatalog/lilcatalog_lang.h

#pragma once

#define LILCATALOG_LANG_H

#define LILCATALOG_S_LANGUAGE                      "uk"
#define LILCATALOG_S_APP                           "ЛілКаталог"

#define LILCATALOG_S_FETCH_CATALOG                 "Оновити каталог"
#define LILCATALOG_S_STOP                          "Вихід"
#define LILCATALOG_S_BACK                          "Назад"
#define LILCATALOG_S_EMPTY                         ""

#define LILCATALOG_S_START                         "Запустити"
#define LILCATALOG_S_INSTALL                       "Встановити"
#define LILCATALOG_S_REMOVE                        "Видалити"
#define LILCATALOG_S_UPDATE                        "Оновити"
#define LILCATALOG_S_ENTRY_DESCRIPTION             "Опис"
#define LILCATALOG_S_LOADING                       "Завантаження"
#define LILCATALOG_S_STARTING                      "Починаємо..."
#define LILCATALOG_S_ENTRY_DESCRIPTION_NAME        "Назва: "
#define LILCATALOG_S_ENTRY_DESCRIPTION_AUTHOR      "Автор: "
#define LILCATALOG_S_ENTRY_DESCRIPTION_DESCRIPTION "Опис: "
#define LILCATALOG_S_ENTRY_DESCRIPTION_FILES       "Файли: "

#define LILCATALOG_S_CATEGORY_POSTFIX              " елементів"
#define LILCATALOG_S_SIZE                          "Розмір:"
#define LILCATALOG_S_FILE_LOADING                  "Завантаження файлу..."
#define LILCATALOG_S_FILE_LOADING_COMPLETE         "Файл завантажено, та збережено"

#define LILCATALOG_S_ERROR_CREATE_FOLDER           "Помилка створення каталогу"
#define LILCATALOG_S_ERROR_NO_CATALOG              "Каталог не знайдено. Завантажте його з інтернету"
#define LILCATALOG_S_ERROR_LOAD_CATALOG            "Помилка завантаження каталогу"
#define LILCATALOG_S_ERROR_FILE_OPEN               "Помилка відкриття файлу"
#define LILCATALOG_S_ERROR_CONNECTION              "Помилка підключення:"
#define LILCATALOG_S_ERROR_DIRETORY_CREATE         "Помилка створення директорії"
#define LILCATALOG_S_ERROR_STAGE1                  "Етап: 1\nКод: "
#define LILCATALOG_S_ERROR_STAGE2                  "Етап: 2\nКод: "
#define LILCATALOG_S_ERROR_STAGE3                  "Етап: 3\nКод: "
#define LILCATALOG_S_SD_NOTFOUND                   "SD карта не знайдена. Неможливо продовжити"
