and3rson/lilka/firmware/keira/src/services/network.h

#pragma once

#include <WiFi.h>
#include "service.h"

#define WIFI_KEIRA_NAMESPACE "kwifi"

enum NetworkState {
    NETWORK_STATE_DISABLED,
    NETWORK_STATE_OFFLINE,
    NETWORK_STATE_CONNECTING,
    NETWORK_STATE_ONLINE,
};

class NetworkService : public Service {
public:
    NetworkService();
    // void configure(String ssid, String password);
    NetworkState getNetworkState();
    int getSignalStrength();
    bool connect(String ssid);
    void connect(String ssid, String password);
    bool getEnabled();
    void setEnabled(bool enabled);

    String getPassword(String ssid);
    String getIpAddr();

private:
    void run() override;
    void autoConnect();
    String hash(String input);
    void setNetworkState(NetworkState state);

    SemaphoreHandle_t mutex;
    NetworkState state;
    int reason;
    int8_t signalStrength; // Value in range [0,3]
    String lastPassword;
    String ipAddr;
};
