and3rson/lilka/firmware/keira/src/apps/liltracker/effects.h

#pragma once

#include <stdint.h>

#include "config.h"

typedef enum : uint8_t {
    EFFECT_TYPE_NONE,
    EFFECT_TYPE_ARPEGGIO, // NES: 00xy
    EFFECT_TYPE_VIBRATO, // NES: 04xy
    EFFECT_TYPE_TREMOLO, // NES: 07xy
    EFFECT_TYPE_VOLUME_SLIDE, // NES: 0Axy
    EFFECT_TYPE_COUNT,
} effect_type_t;

const effect_type_t effects[EFFECT_TYPE_COUNT] = {
    EFFECT_TYPE_NONE,
    EFFECT_TYPE_ARPEGGIO,
    EFFECT_TYPE_VIBRATO,
    EFFECT_TYPE_TREMOLO,
    EFFECT_TYPE_VOLUME_SLIDE,
};

const char effect_signs[EFFECT_TYPE_COUNT] = {
    '.',
    'A',
    'V',
    'T',
    'S',
};

typedef struct {
    effect_type_t type;
    uint8_t param;
} PACKED effect_t;

typedef void (*effect_fn_t)(
    const float time, const float relTime, float* frequency, float* amplitude, float* phase, uint8_t param
);

void effect_none(
    const float time, const float relTime, float* frequency, float* amplitude, float* phase, uint8_t param
);
void effect_arpeggio(
    const float time, const float relTime, float* frequency, float* amplitude, float* phase, uint8_t param
);
void effect_vibrato(
    const float time, const float relTime, float* frequency, float* amplitude, float* phase, uint8_t param
);
void effect_tremolo(
    const float time, const float relTime, float* frequency, float* amplitude, float* phase, uint8_t param
);
void effect_volume_slide(
    const float time, const float relTime, float* frequency, float* amplitude, float* phase, uint8_t param
);

const effect_fn_t effect_functions[EFFECT_TYPE_COUNT] = {
    effect_none,
    effect_arpeggio,
    effect_vibrato,
    effect_tremolo,
    effect_volume_slide,
};
