and3rson/lilka/firmware/keira/src/service.cpp

#include "service.h"

Service::Service(const char* name) : name(name), taskHandle(NULL), stackSize(8192) {
}

Service::~Service() {
}

void Service::start() {
    lilka::serial_log("Starting service %s", name);
    xTaskCreate(_run, name, stackSize, this, 1, &taskHandle);
}

void Service::_run(void* arg) {
    Service* service = static_cast<Service*>(arg);
    service->run();
    lilka::serial_err("Service %s died", service->name);
}

void Service::setStackSize(uint32_t stackSize) {
    this->stackSize = stackSize;
}
