and3rson/lilka/firmware/keira/src/servicemanager.h

#pragma once

#include "service.h"

class AcquireServiceManager {
public:
    explicit AcquireServiceManager(SemaphoreHandle_t xMutex) : xMutex(xMutex) {
        xSemaphoreTake(xMutex, portMAX_DELAY);
    }
    ~AcquireServiceManager() {
        xSemaphoreGive(xMutex);
    }

private:
    SemaphoreHandle_t xMutex;
};

class ServiceManager {
public:
    ~ServiceManager();
    void addService(Service* service);

    template <typename T>
    T* getService(const char* name) {
        AcquireServiceManager acquire(xMutex);
        std::vector<Service*>::iterator it =
            std::find_if(services.begin(), services.end(), [name](const Service* service) {
                return strcmp(service->name, name) == 0;
            });
        if (it != services.end()) {
            return static_cast<T*>(*it);
        }
        lilka::serial_err("getService(): service %s not found", name);
        return nullptr;
    }

    static ServiceManager* getInstance();

private:
    ServiceManager();
    static ServiceManager* instance;
    std::vector<Service*> services;
    SemaphoreHandle_t xMutex;
};
