and3rson/lilka/firmware/keira/src/apps/demos/letris.cpp

#include "letris.h"
#include "letris_splash.h"

#define BLOCK_SIZE 10
#define FIELD_COLS 10
#define FIELD_ROWS 21

const bool shapesData[7][4][4] = {
    {{0, 1, 0, 0}, {0, 1, 0, 0}, {0, 1, 0, 0}, {0, 1, 0, 0}}, // I
    {{0, 0, 0, 0}, {0, 1, 1, 0}, {0, 1, 1, 0}, {0, 0, 0, 0}}, // O
    {{0, 0, 0, 0}, {0, 1, 1, 0}, {1, 1, 0, 0}, {0, 0, 0, 0}}, // S
    {{0, 0, 0, 0}, {1, 1, 0, 0}, {0, 1, 1, 0}, {0, 0, 0, 0}}, // Z
    {{0, 0, 0, 0}, {1, 1, 1, 0}, {0, 1, 0, 0}, {0, 0, 0, 0}}, // T
    {{0, 1, 0, 0}, {0, 1, 0, 0}, {0, 1, 1, 0}, {0, 0, 0, 0}}, // L
    {{0, 0, 1, 0}, {0, 0, 1, 0}, {0, 1, 1, 0}, {0, 0, 0, 0}}, // J
};

const uint16_t colors[7] = {
    lilka::colors::Red,
    lilka::colors::Green,
    lilka::colors::Blue,
    lilka::colors::Yellow,
    lilka::colors::Fuchsia,
    lilka::colors::Aqua,
    lilka::colors::Light_gray,
};
const uint8_t colorCount = sizeof(colors) / sizeof(colors[0]);

class Shape {
public:
    int x, y;
    int shapeData[4][4];
    uint16_t color;

    Shape() : x(0), y(0), shapeData(), color(0) {
    }

    void reset() {
        // Генерує нову фігуру. Нові фігури відображаються в вікні попереднього перегляду
        x = FIELD_COLS + 2;
        y = 2;
        uint8_t shapeIndex = random(0, 7);
        for (int i = 0; i < 4; i++) {
            for (int j = 0; j < 4; j++) {
                this->shapeData[i][j] = shapesData[shapeIndex][i][j];
            }
        }
        color = colors[random(0, colorCount)];
    }

    void moveToField() {
        // Переміщує фігуру в поле
        x = FIELD_COLS / 2 - 2;
        y = 0;
    }

    void draw(lilka::Canvas* canvas, bool drawEmptyBlocks = false) {
        int16_t xOffset = canvas->width() / 2 - FIELD_COLS * BLOCK_SIZE / 2;
        for (int yy = 0; yy < 4; yy++) {
            for (int xx = 0; xx < 4; xx++) {
                if (this->shapeData[yy][xx]) {
                    canvas->fillRect(
                        xOffset + (this->x + xx) * BLOCK_SIZE,
                        (this->y + yy) * BLOCK_SIZE,
                        BLOCK_SIZE,
                        BLOCK_SIZE,
                        color
                    );
                    canvas->fillRect(
                        xOffset + (this->x + xx) * BLOCK_SIZE + 2,
                        (this->y + yy) * BLOCK_SIZE + 2,
                        BLOCK_SIZE - 4,
                        BLOCK_SIZE - 4,
                        lilka::colors::Black
                    );
                } else if (drawEmptyBlocks) {
                    canvas->fillRect(
                        xOffset + (this->x + xx) * BLOCK_SIZE,
                        (this->y + yy) * BLOCK_SIZE,
                        BLOCK_SIZE,
                        BLOCK_SIZE,
                        lilka::colors::Black
                    );
                }
            }
        }
    }

    bool canMove(int dx, int dy) {
        // TODO
        return true;
    }

    void move(int dx, int dy) {
        if (this->canMove(dx, dy)) {
            this->x += dx;
            this->y += dy;
        }
    }

    void rotate() {
        // Rotate shape right
        int newShapeData[4][4];
        for (int i = 0; i < 4; i++) {
            for (int j = 0; j < 4; j++) {
                newShapeData[i][j] = this->shapeData[3 - j][i];
            }
        }
        for (int i = 0; i < 4; i++) {
            for (int j = 0; j < 4; j++) {
                this->shapeData[i][j] = newShapeData[i][j];
            }
        }
    }
};

class Field {
public:
    Field() {
        for (int y = 0; y < FIELD_ROWS; y++) {
            for (int x = 0; x < FIELD_COLS; x++) {
                this->blocks[y][x] = 0;
            }
        }
    }
    void draw(lilka::Canvas* canvas) {
        // Малює поле
        int16_t xOffset = canvas->width() / 2 - FIELD_COLS * BLOCK_SIZE / 2;
        for (int y = 0; y < FIELD_ROWS; y++) {
            for (int x = 0; x < FIELD_COLS; x++) {
                canvas->fillRect(xOffset + x * BLOCK_SIZE, y * BLOCK_SIZE, BLOCK_SIZE, BLOCK_SIZE, this->blocks[y][x]);
            }
        }
    }
    void addShape(const Shape* shape) {
        // Додає фігуру як частину поля
        for (int yy = 0; yy < 4; yy++) {
            for (int xx = 0; xx < 4; xx++) {
                if (shape->shapeData[yy][xx]) {
                    this->blocks[shape->y + yy][shape->x + xx] = shape->color;
                }
            }
        }
        // Перевіряємо, чи є рядки, які можна видалити
        for (int y = 0; y < FIELD_ROWS; y++) {
            bool full = true;
            for (int x = 0; x < FIELD_COLS; x++) {
                if (!this->blocks[y][x]) {
                    full = false;
                    break;
                }
            }
            if (full) {
                // Видаляємо рядок
                for (int yy = y; yy > 0; yy--) {
                    for (int xx = 0; xx < FIELD_COLS; xx++) {
                        this->blocks[yy][xx] = this->blocks[yy - 1][xx];
                    }
                }
                for (int xx = 0; xx < FIELD_COLS; xx++) {
                    this->blocks[0][xx] = 0;
                }
            }
        }
    }
    bool willCollide(const Shape* shape, int dx, int dy) {
        // Повертає true, якщо фігура зіткнеться з іншими блоками, якщо зміститься на (dx, dy)
        for (int yy = 0; yy < 4; yy++) {
            for (int xx = 0; xx < 4; xx++) {
                if (shape->shapeData[yy][xx]) {
                    if (shape->x + xx + dx < 0 || shape->x + xx + dx >= FIELD_COLS ||
                        shape->y + yy + dy >= FIELD_ROWS || this->blocks[shape->y + yy + dy][shape->x + xx + dx]) {
                        return true;
                    }
                }
            }
        }
        return false;
    }
    bool canRotate(const Shape* shape) {
        // Створюємо новий масив для фігури після повороту
        int newShapeData[4][4];
        for (int i = 0; i < 4; i++) {
            for (int j = 0; j < 4; j++) {
                newShapeData[i][j] = shape->shapeData[3 - j][i];
            }
        }
        // Перевіряємо, чи нова позиція фігури після повороту зіткнеться з іншими блоками
        for (int yy = 0; yy < 4; yy++) {
            for (int xx = 0; xx < 4; xx++) {
                if (newShapeData[yy][xx]) {
                    if (shape->x + xx < 0 || shape->x + xx >= FIELD_COLS || shape->y + yy >= FIELD_ROWS ||
                        this->blocks[shape->y + yy][shape->x + xx]) {
                        return false; // Поворот неможливий
                    }
                }
            }
        }
        return true; // Поворот можливий
    }

private:
    uint16_t blocks[FIELD_ROWS][FIELD_COLS]; // Black color means no block
};

LetrisApp::LetrisApp() : App("Letris") {
}
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
